hannahrosen57/AdjustaBike-2.0/CAD/exportedCAD/bike.pdf

setPageBoxes("Crop", 0, 0, [0,2000,2000,0]);
TITLE PART NO | bike REVISION DESIGNER | Hannah ENGINEER NOTES

THE INFORMATION AND/OR MATERIAL IN THIS DOCUMENT IS THE PROPERTY OF AND RESTRICTED INFORMATION AND/OR MATERIAL OF THE AUTHOR. THIS INFORMATION MAY NOT BE USED, REPRODUCED, PUBLISHED OR DISCLOSED TO OTHERS WITHOUT WRITTEN AUTHORIZATION. IT IS TO BE USED ONLY FOR MANUFACTURING ITEMS SPECIFIED WITHIN THE DOCUMENT.
