hannahrosen57/AdjustaBike-2.0/PSP/health and safety completed.pdf

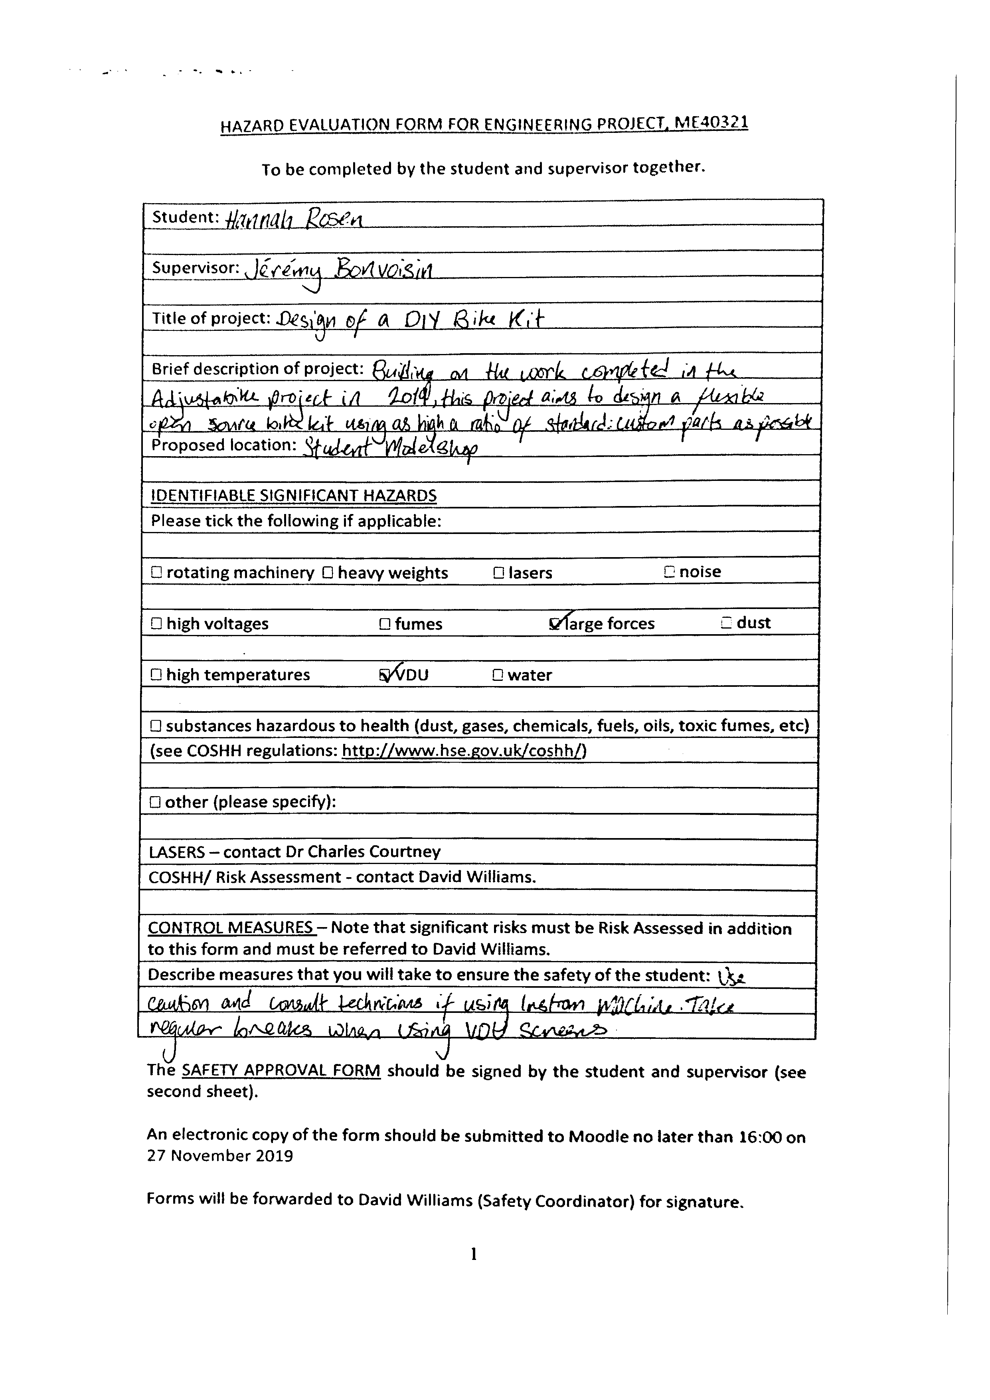
[picture p164: page 1]
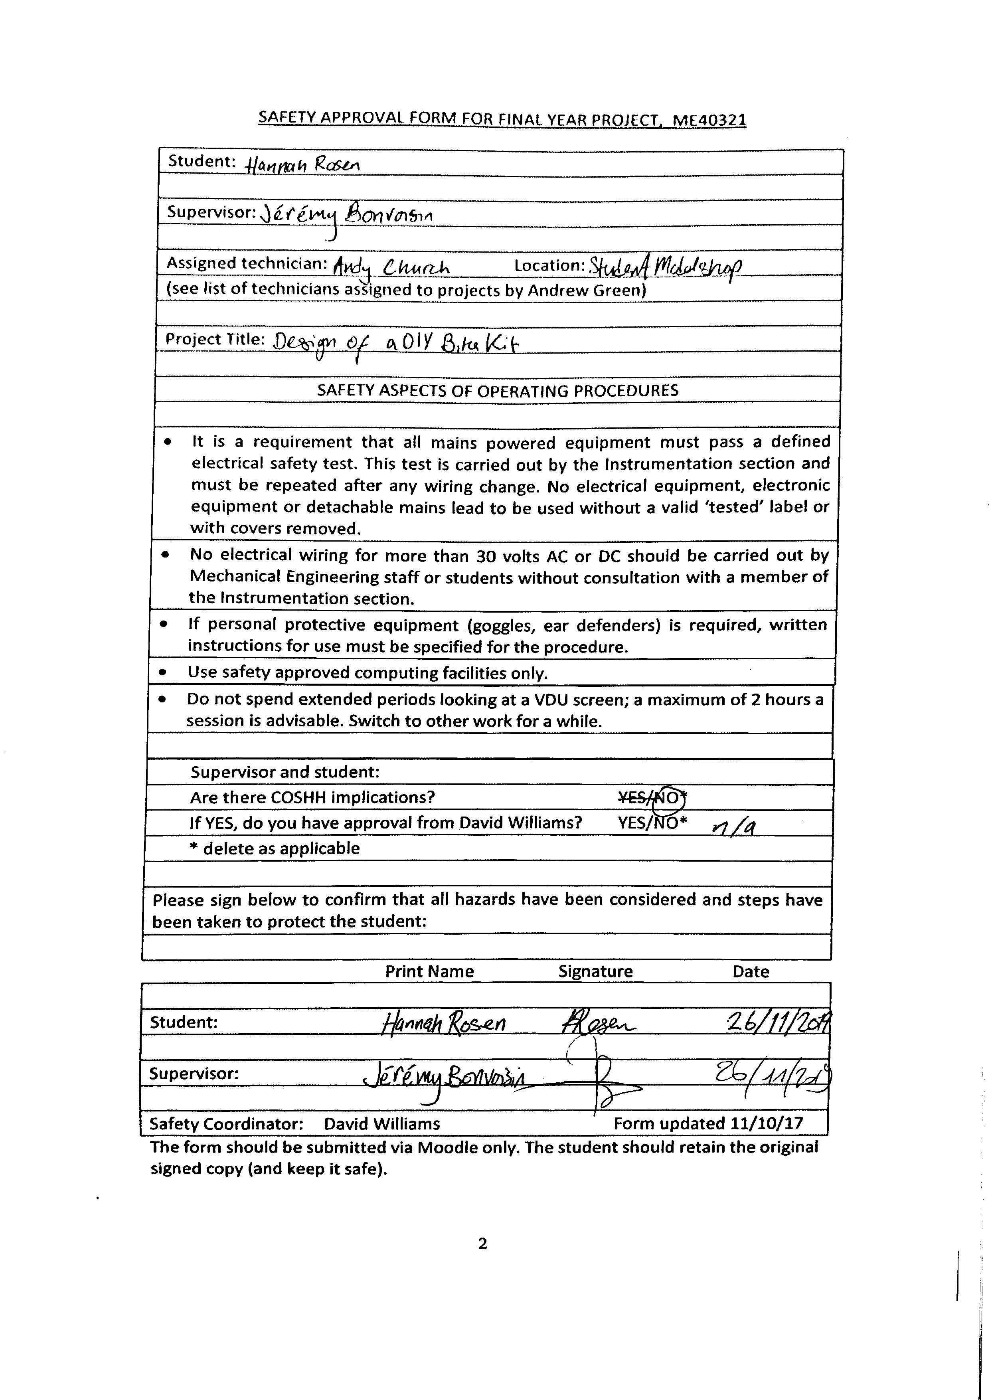
[picture p165: page 2]
