hannahrosen57/AdjustaBike-2.0/CAD/bicycle-wheel-tire-26-inch/2.jpg

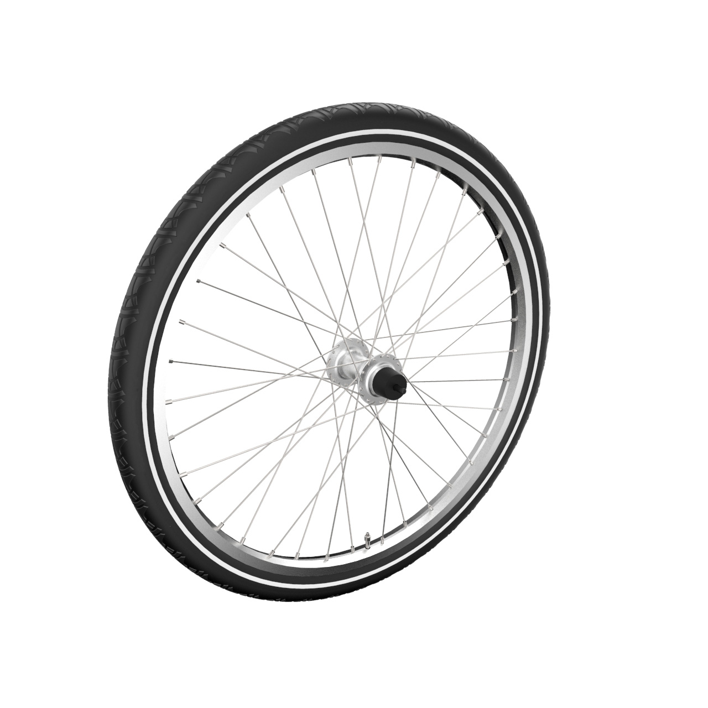
CAD/bicycle-wheel-tire-26-inch/2.jpg
