hannahrosen57/AdjustaBike-2.0/CAD/LW bike.png

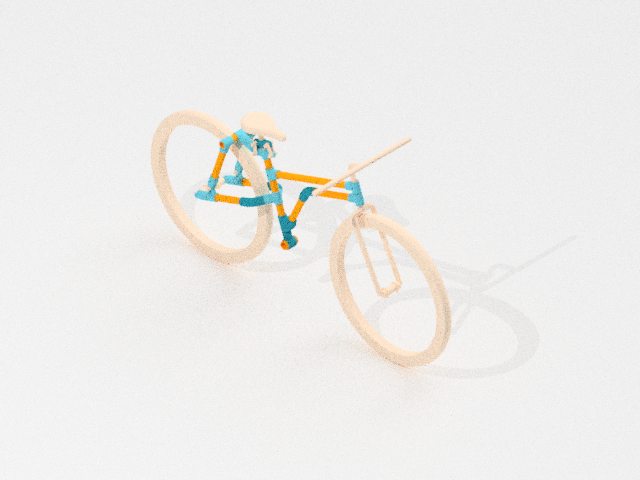
CAD/LW bike.png
