hannahrosen57/AdjustaBike-2.0/CAD/renders/LW bike 1.png

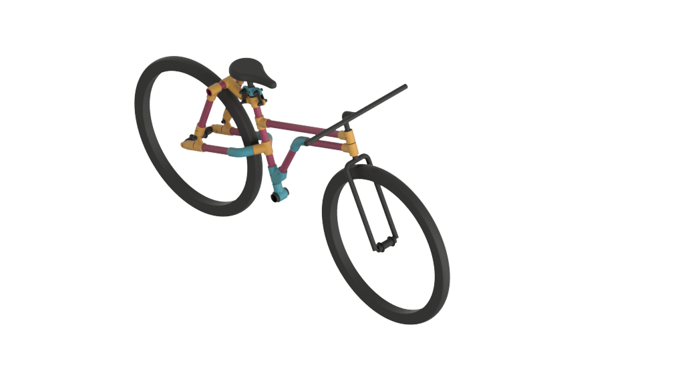
CAD/renders/LW bike 1.png
