hannahrosen57/AdjustaBike-2.0/CAD/renders/LW bike 5.png

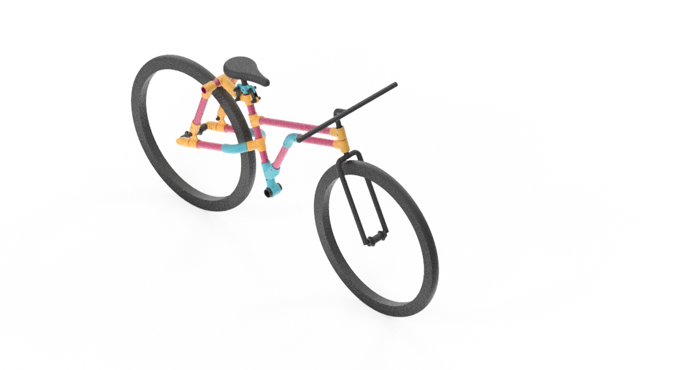
CAD/renders/LW bike 5.png
