hannahrosen57/AdjustaBike-2.0/CAD/Screen Shot 2020-05-14 at 21.41.56.png

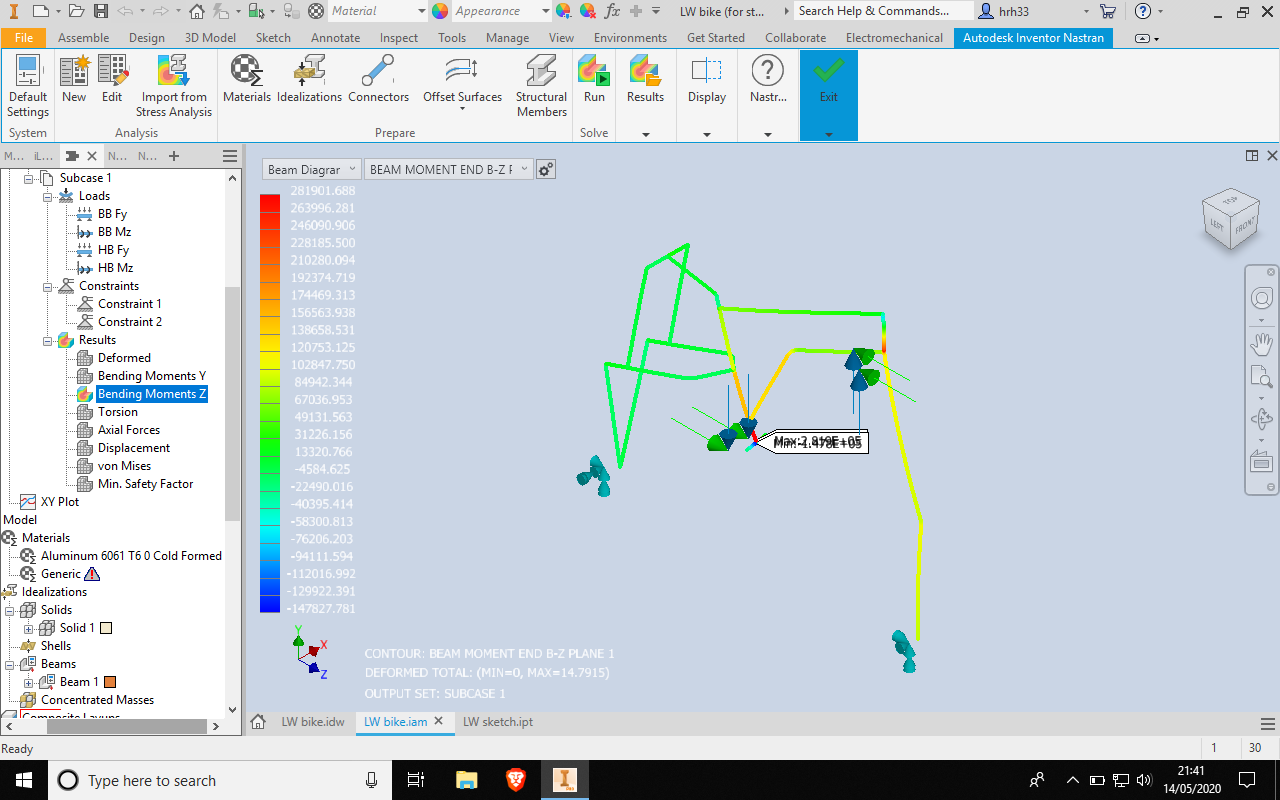
CAD/Screen Shot 2020-05-14 at 21.41.56.png
