hannahrosen57/AdjustaBike-2.0/CAD/screenshots/angle tee.png

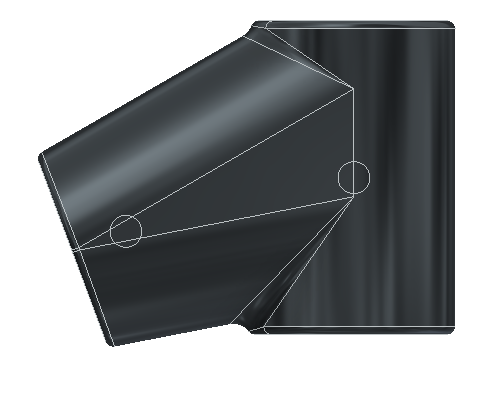
CAD/screenshots/angle tee.png
