hannahrosen57/AdjustaBike-2.0/CAD/screenshots/axial forces.png

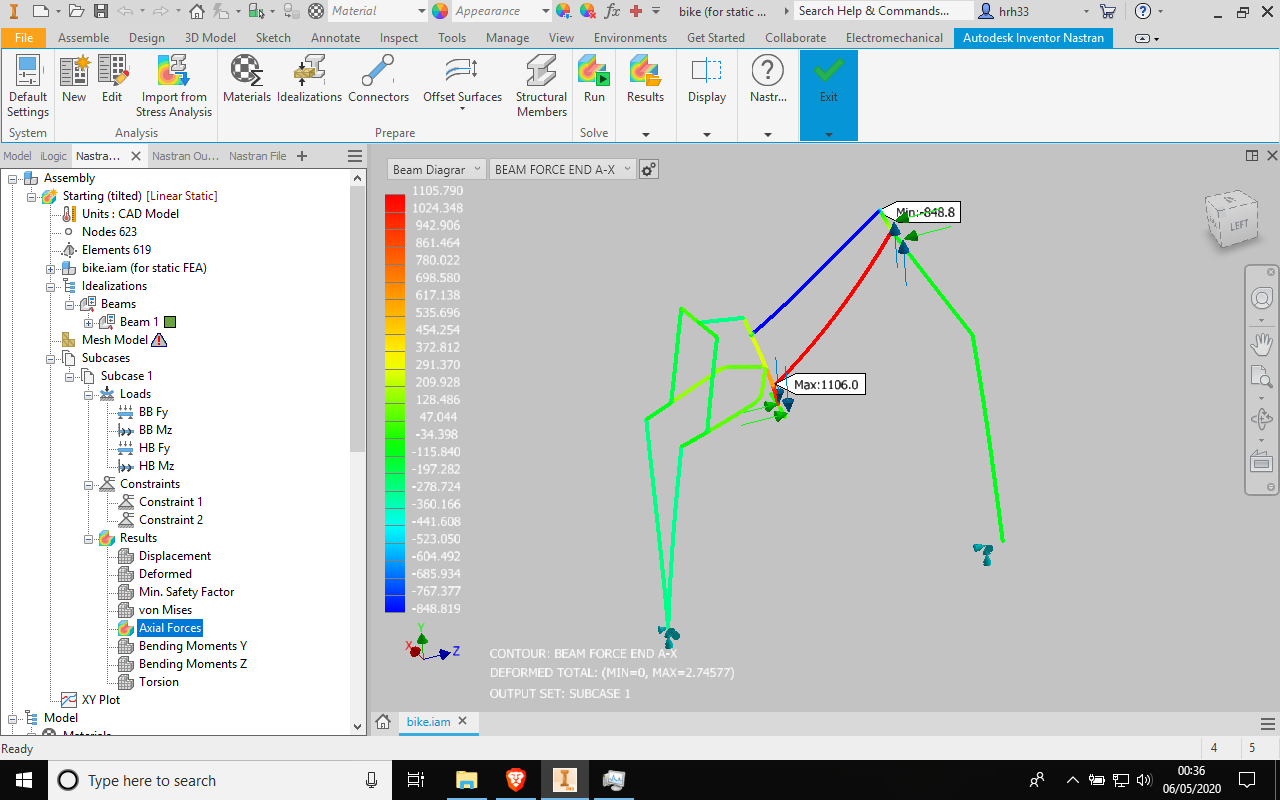
CAD/screenshots/axial forces.png
