hannahrosen57/AdjustaBike-2.0/CAD/screenshots/bike mesh.png

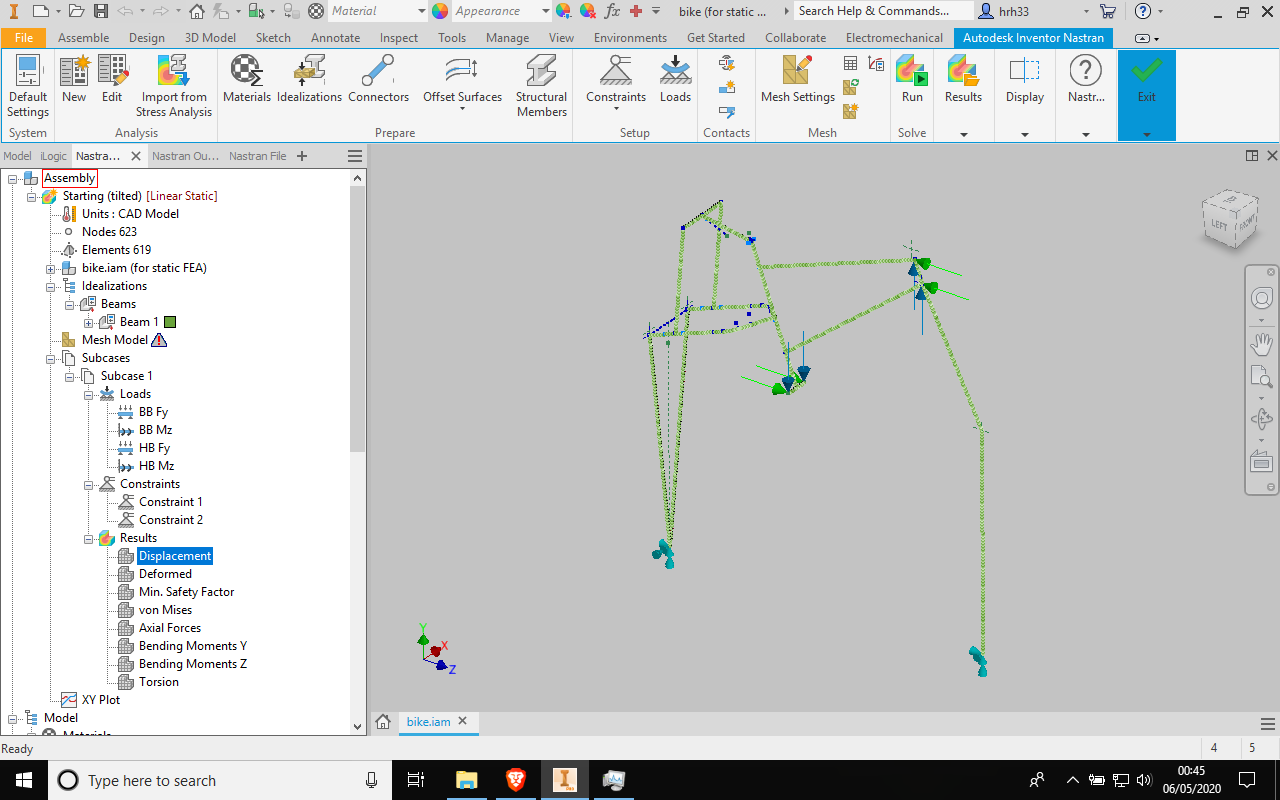
CAD/screenshots/bike mesh.png
