hannahrosen57/AdjustaBike-2.0/CAD/screenshots/disp.png

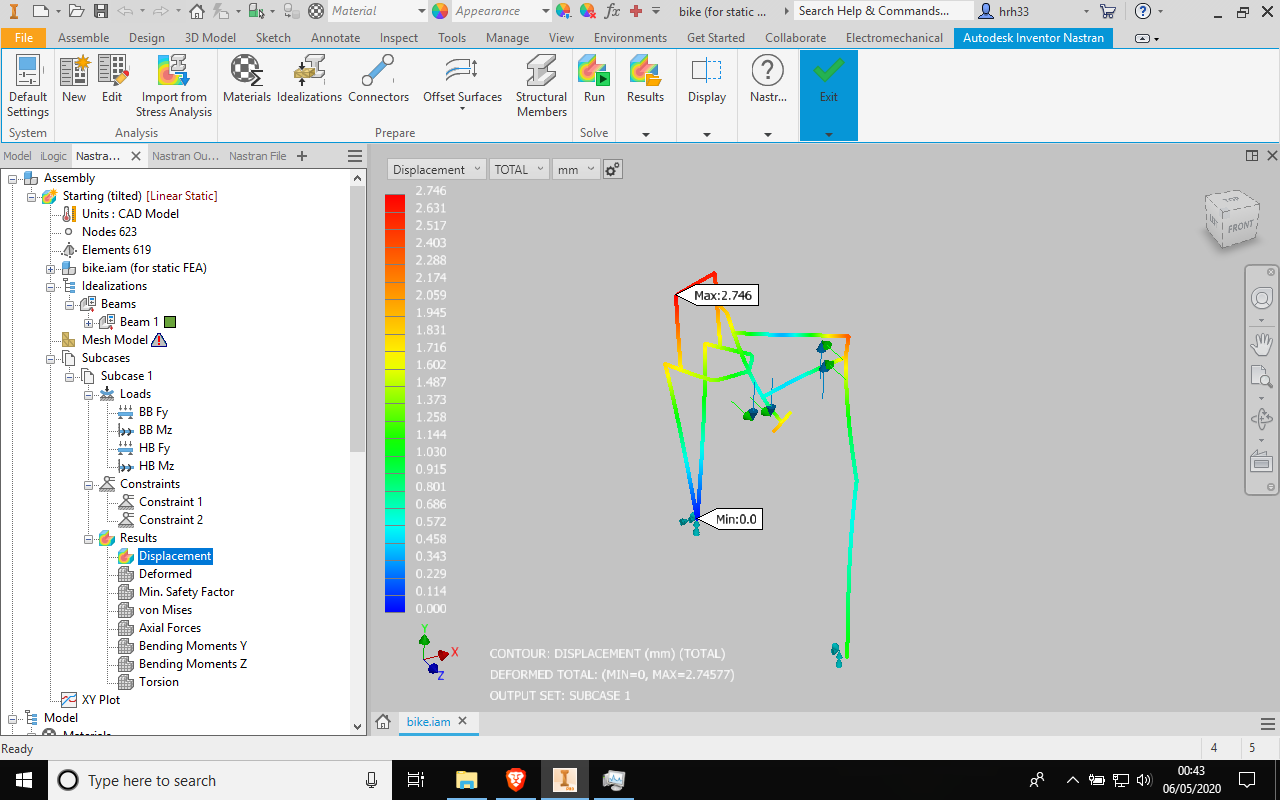
CAD/screenshots/disp.png
