hannahrosen57/AdjustaBike-2.0/CAD/screenshots/open part files.png

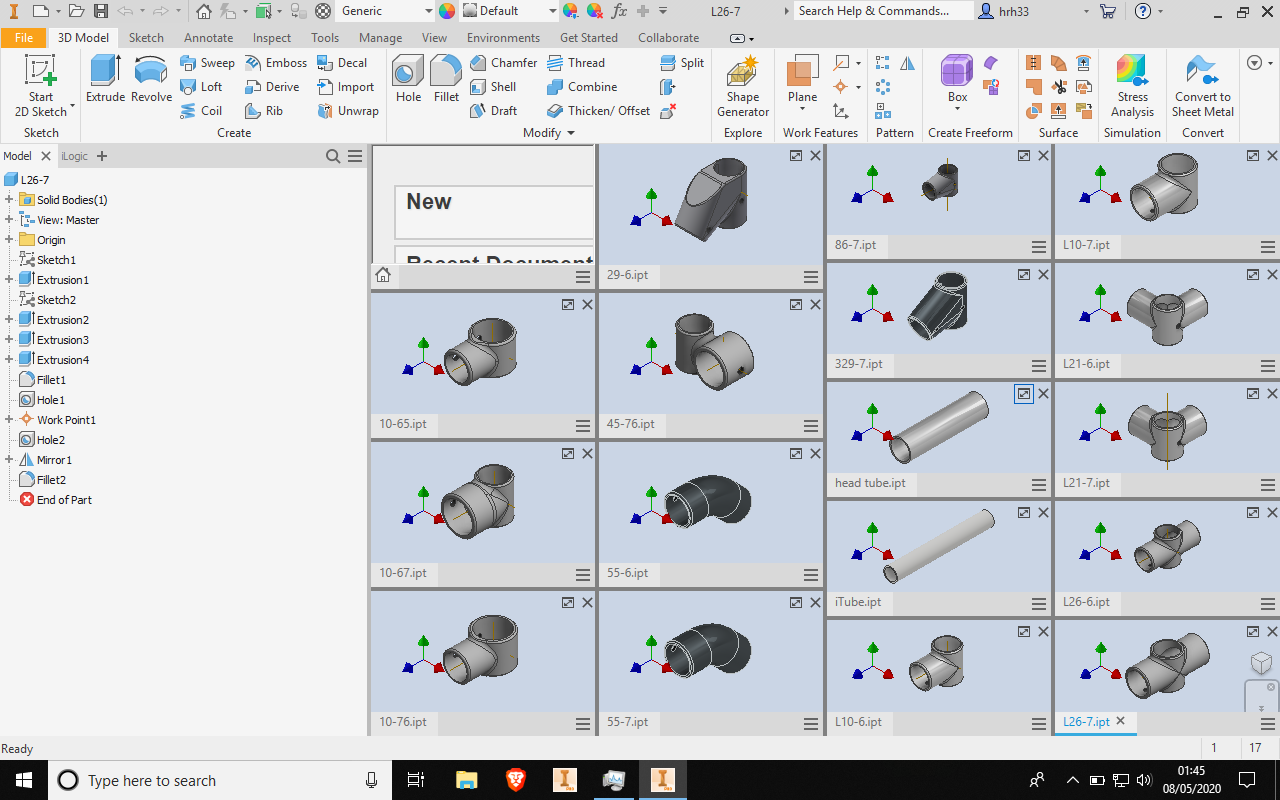
CAD/screenshots/open part files.png
