hannahrosen57/AdjustaBike-2.0/CAD/screenshots/sf closeup.png

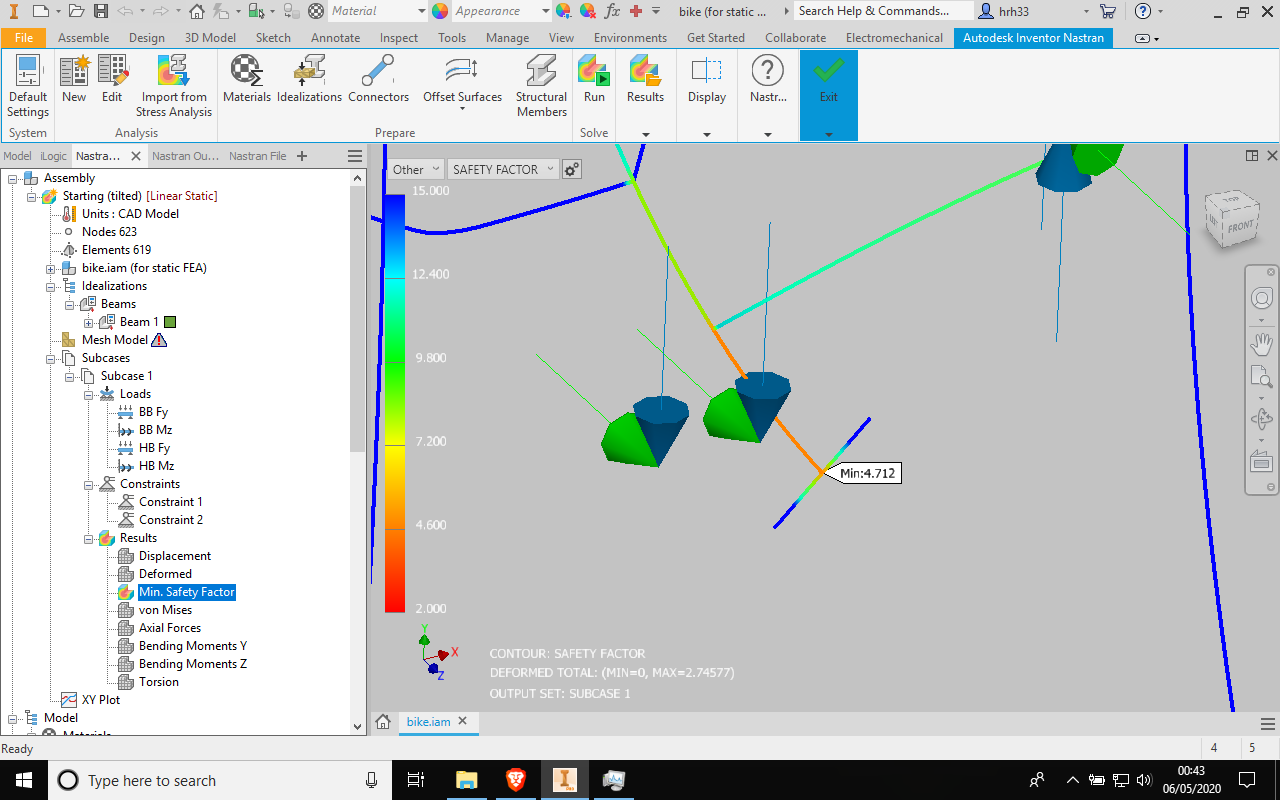
CAD/screenshots/sf closeup.png
