hannahrosen57/AdjustaBike-2.0/CAD/screenshots/sf.png

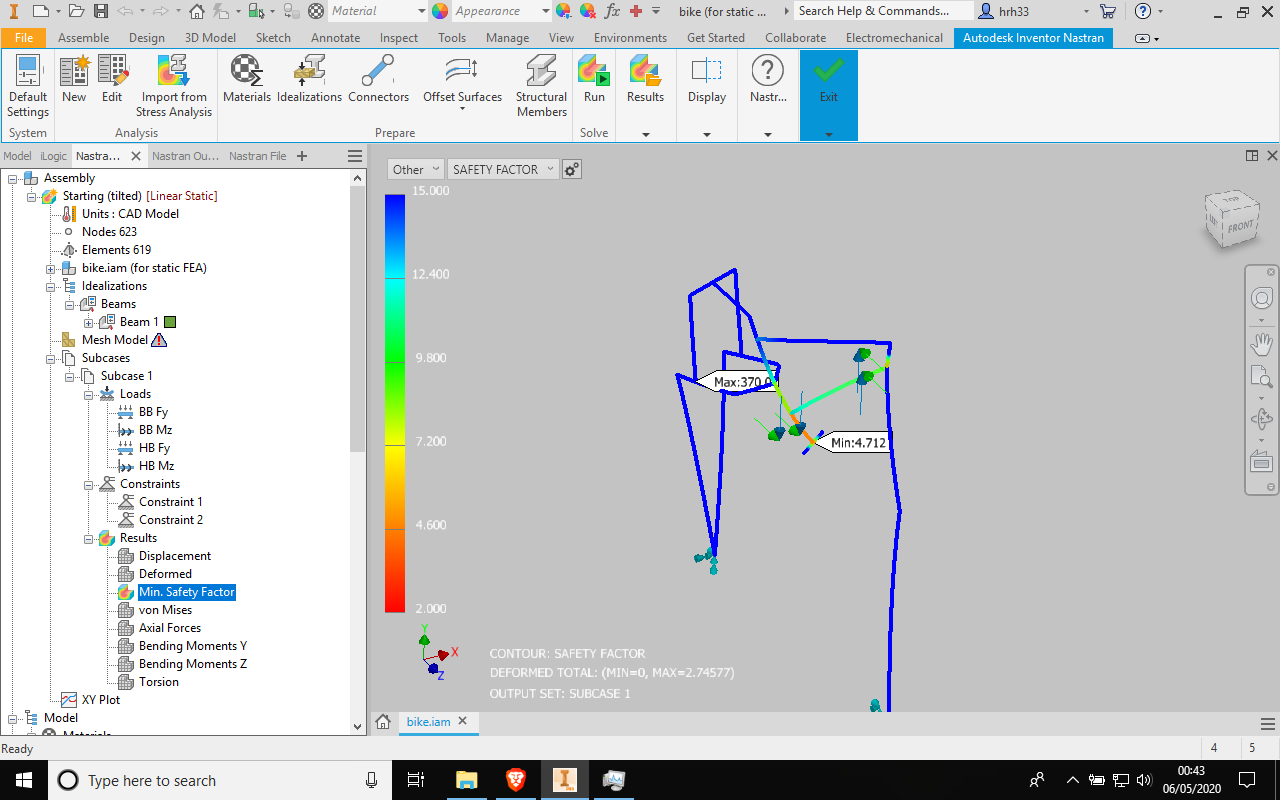
CAD/screenshots/sf.png
