hannahrosen57/AdjustaBike-2.0/CAD/screenshots/von mises 4.png

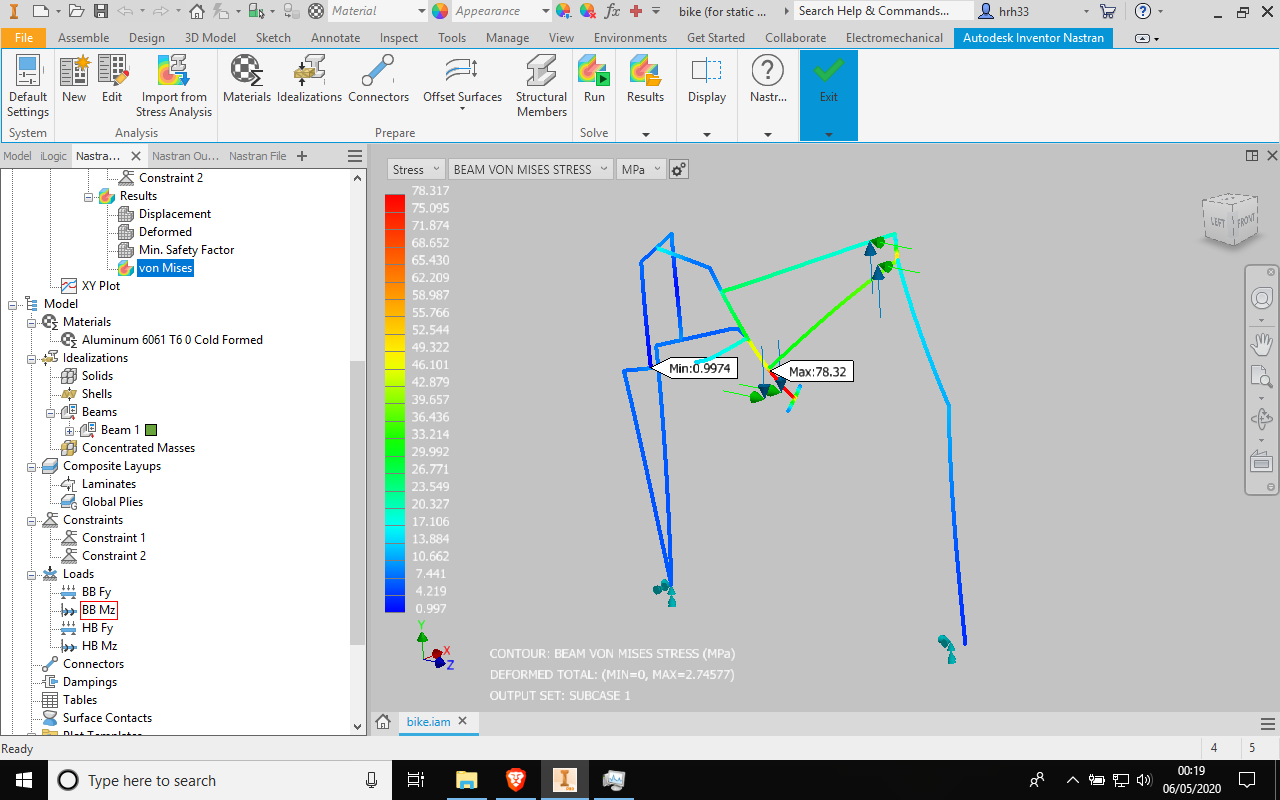
CAD/screenshots/von mises 4.png
