hannahrosen57/AdjustaBike-2.0/CAD/screenshots/von mises bike 1.png

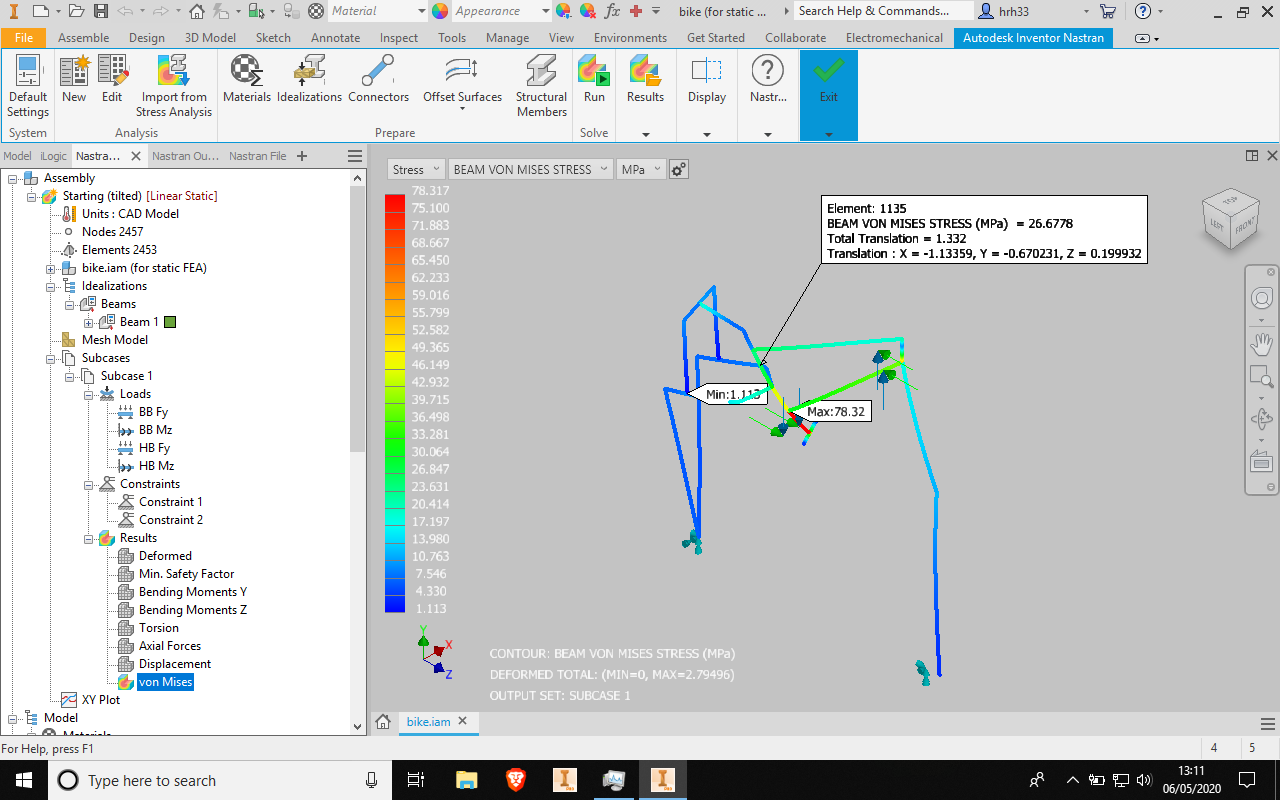
CAD/screenshots/von mises bike 1.png
