hannahrosen57/AdjustaBike-2.0/CAD/screenshots/von mises bike front.png

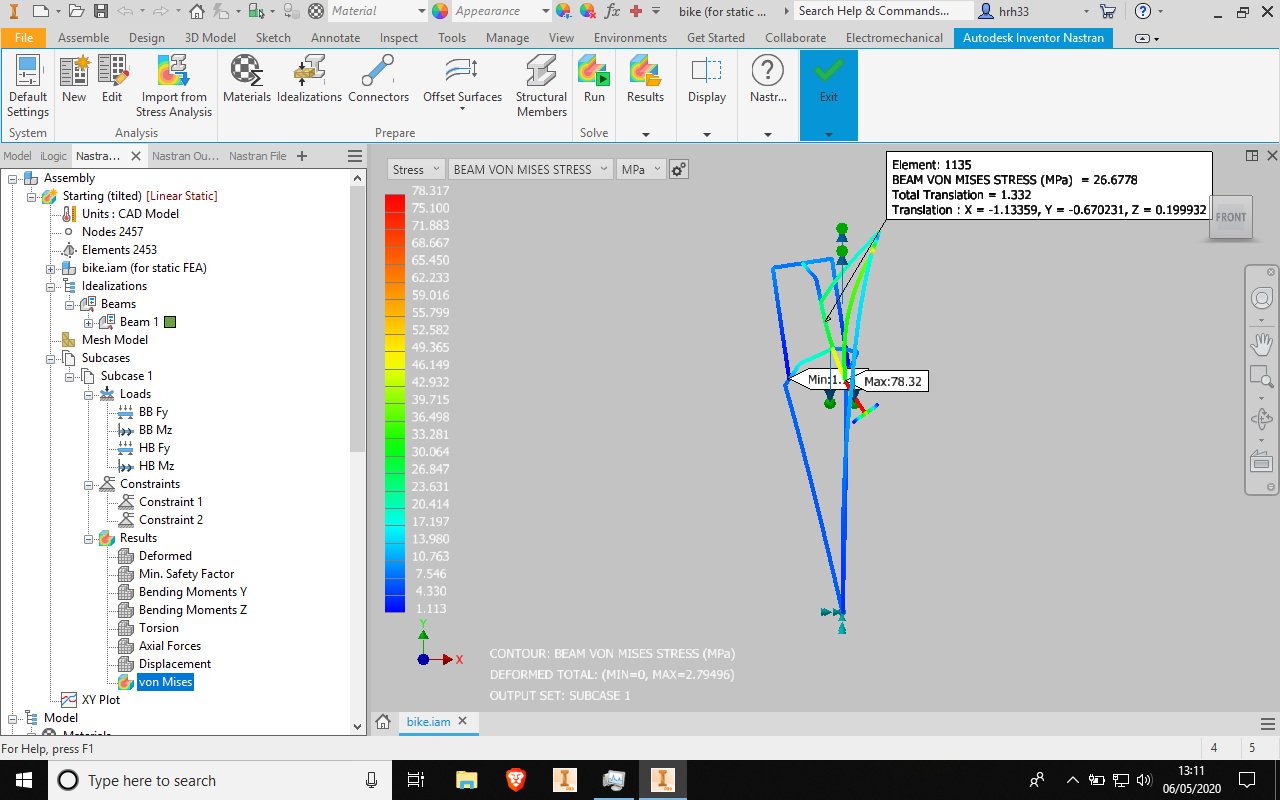
CAD/screenshots/von mises bike front.png
