hannahrosen57/AdjustaBike-2.0/clutter/bicycle frame geometries.png

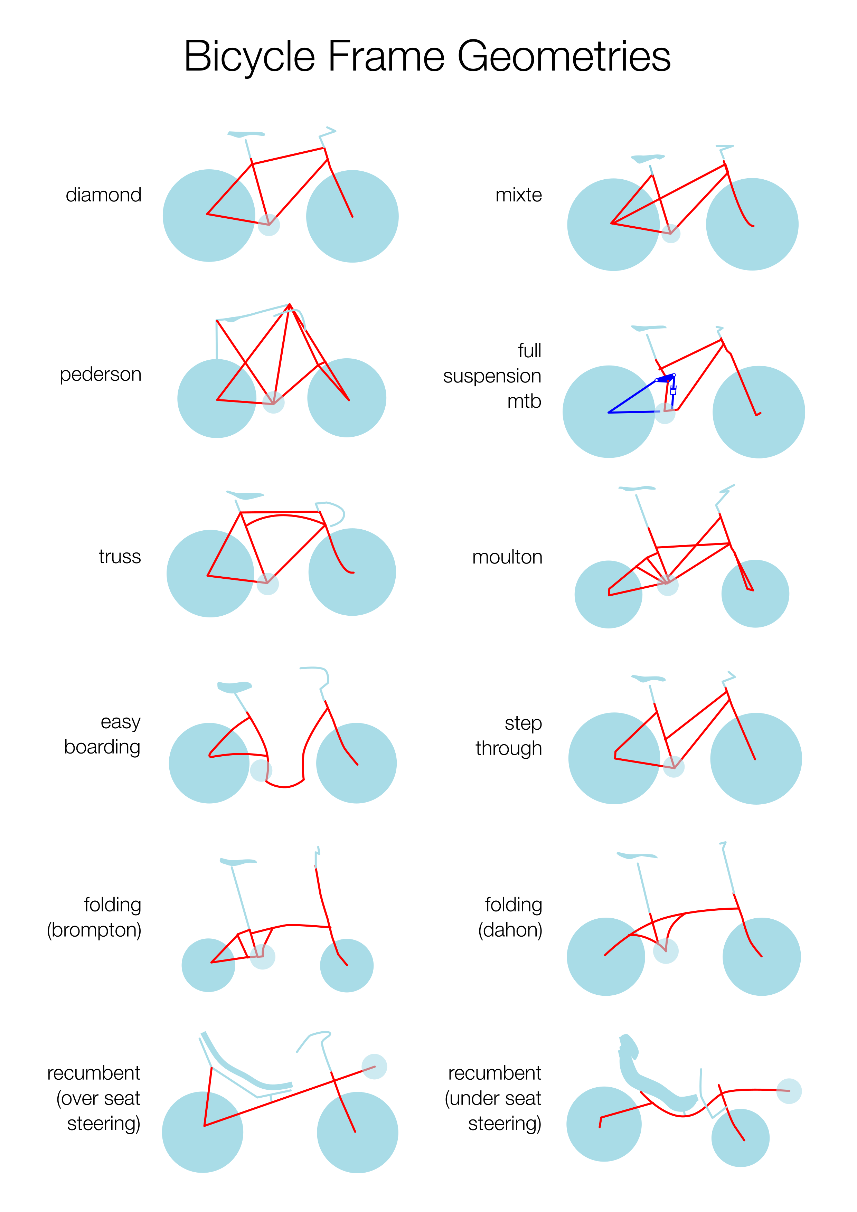
clutter/bicycle frame geometries.png
