hannahrosen57/AdjustaBike-2.0/clutter/cropped_fea1.png

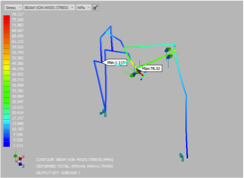
clutter/cropped_fea1.png
