hannahrosen57/AdjustaBike-2.0/clutter/cropped_FEA2.png

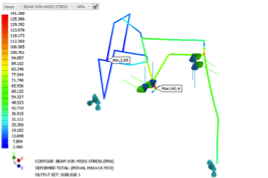
clutter/cropped_FEA2.png
