hannahrosen57/AdjustaBike-2.0/clutter/DIY frame geometries.png

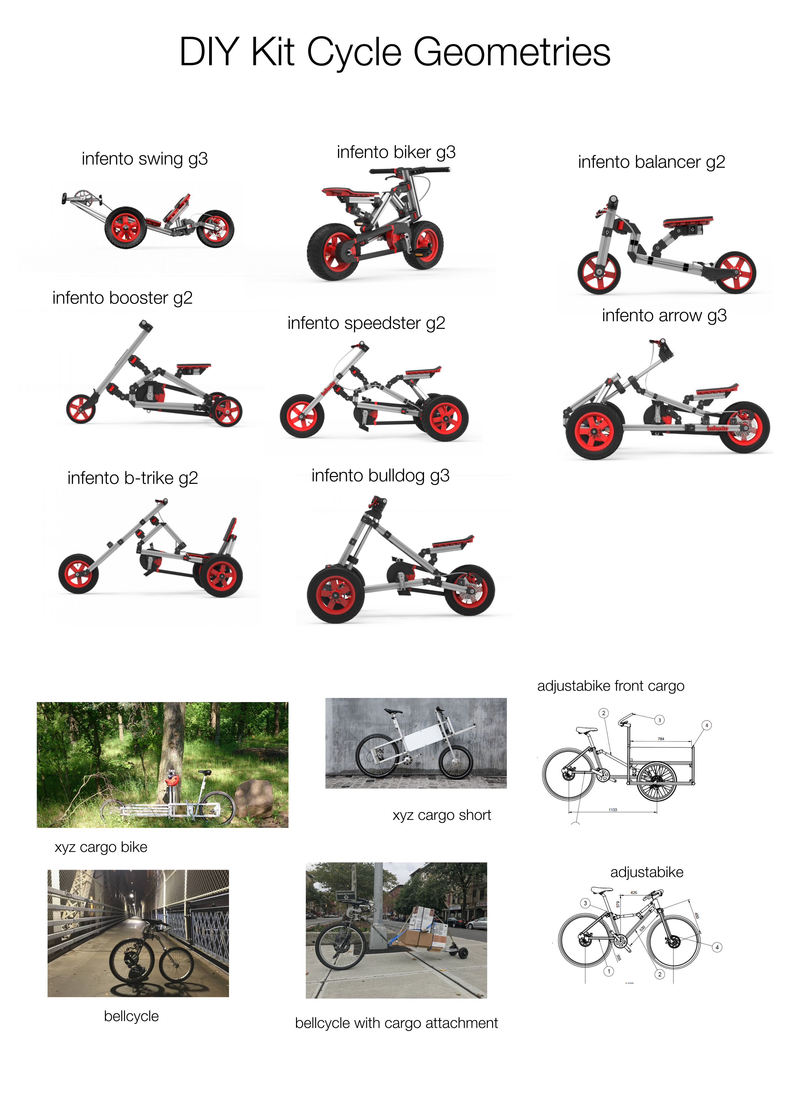
clutter/DIY frame geometries.png
