hannahrosen57/AdjustaBike-2.0/PSP/images/b-trike07-690x449.jpg

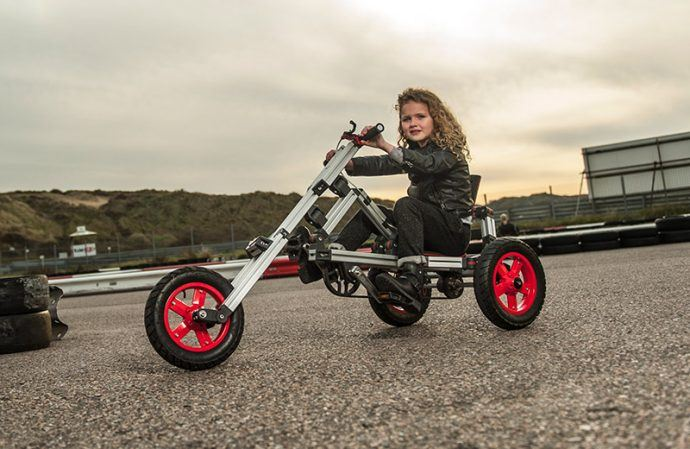
PSP/images/b-trike07-690x449.jpg
