hannahrosen57/AdjustaBike-2.0/PSP/images/bellcycle.PNG

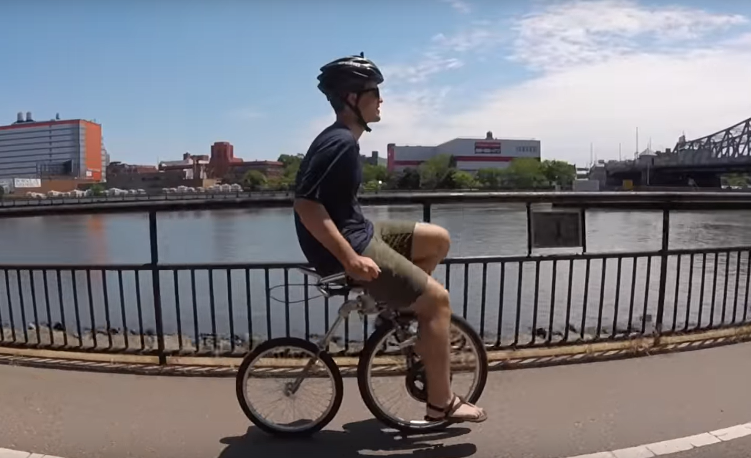
PSP/images/bellcycle.PNG
