hannahrosen57/AdjustaBike-2.0/PSP/images/bulldog12-690x449.jpg

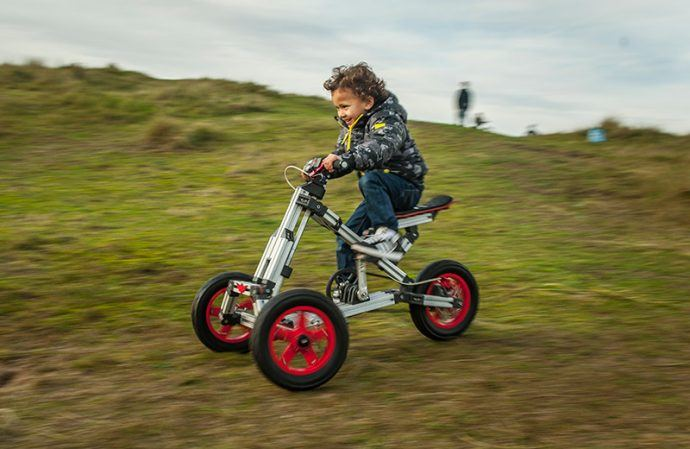
PSP/images/bulldog12-690x449.jpg
