hannahrosen57/AdjustaBike-2.0/PSP/images/obi-bike-flip.png

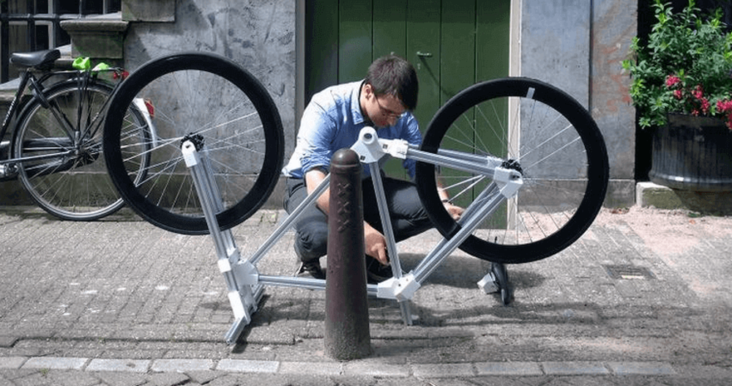
PSP/images/obi-bike-flip.png
