hannahrosen57/AdjustaBike-2.0/PSP/images/parameters.PNG

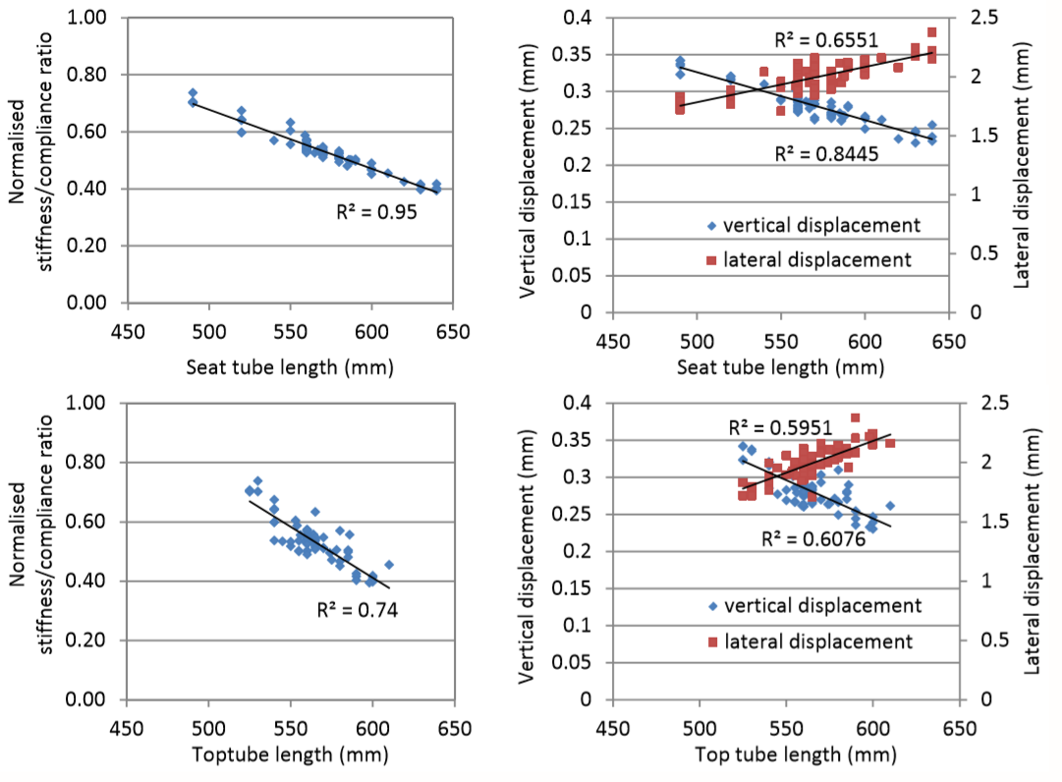
PSP/images/parameters.PNG
