hannahrosen57/AdjustaBike-2.0/PSP/images/skywalker.PNG

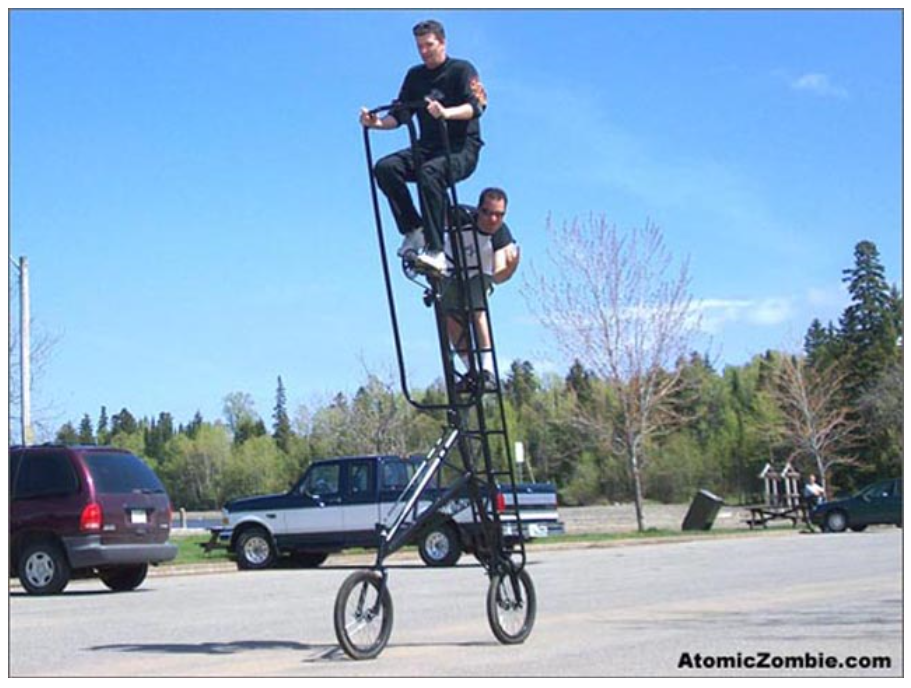
PSP/images/skywalker.PNG
