hannahrosen57/AdjustaBike-2.0/PSP/images/velocar.jpg

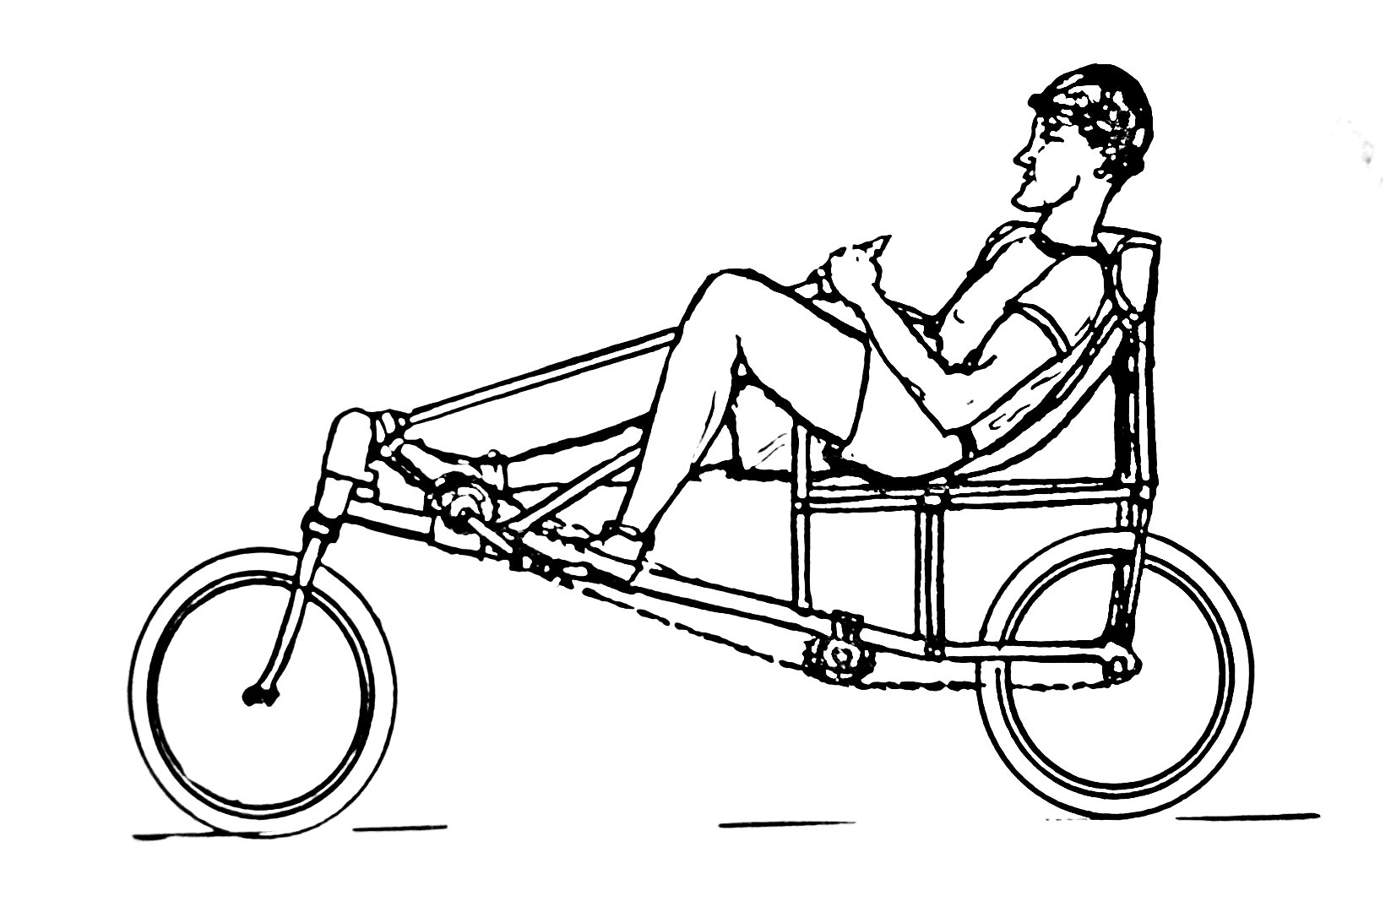
PSP/images/velocar.jpg
