hannahrosen57/AdjustaBike-2.0/PSP/images/XYZ-CARGO-Group1.jpg

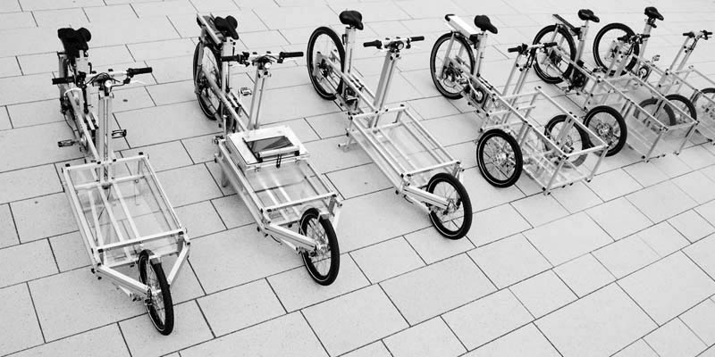
PSP/images/XYZ-CARGO-Group1.jpg
