hannahrosen57/AdjustaBike-2.0/clutter/possible components/Q-CLAMP-JINAN-TUV-LOAD-TABLE-3.pdf

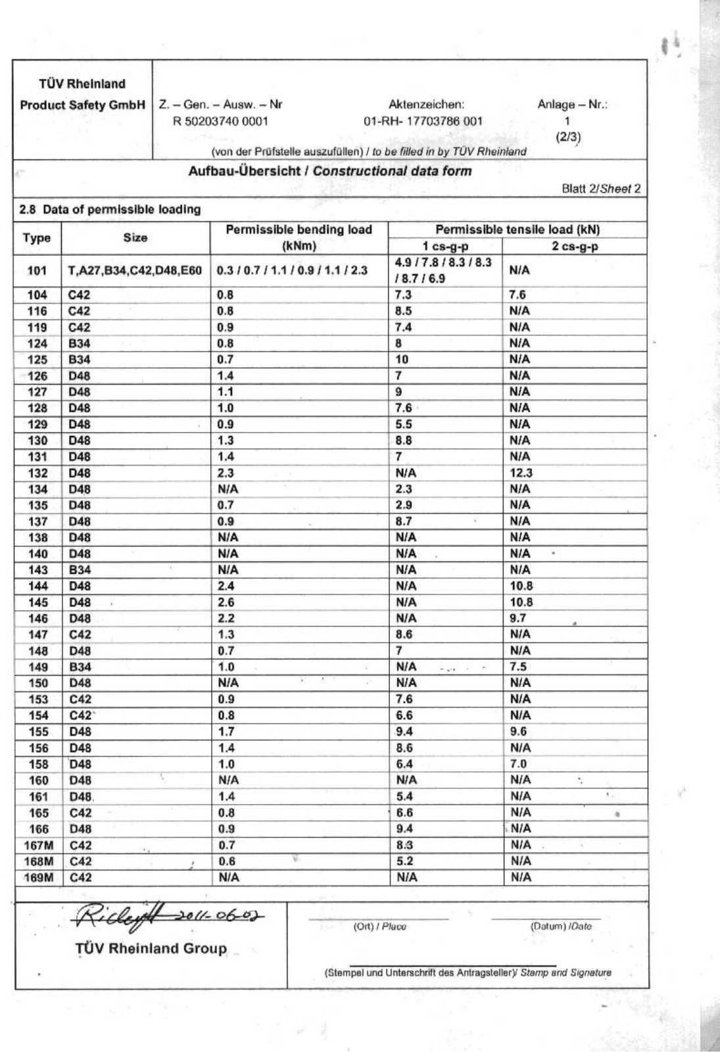
[picture p201: page 1]
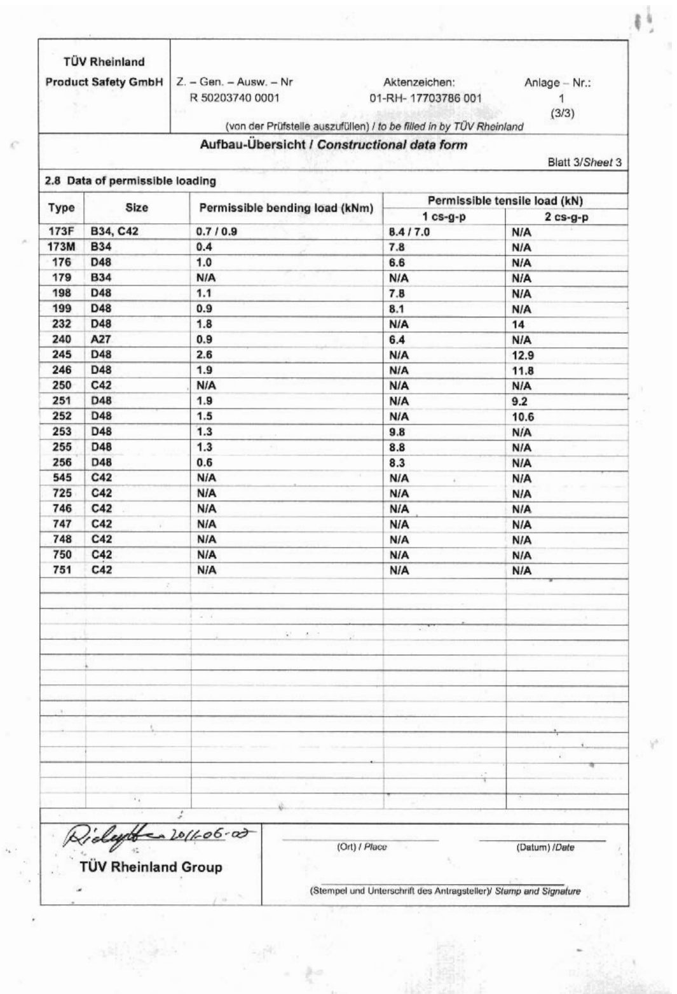
[picture p202: page 2]
