hannahrosen57/AdjustaBike-2.0/clutter/possible components/Qclamp-conversion-table.pdf

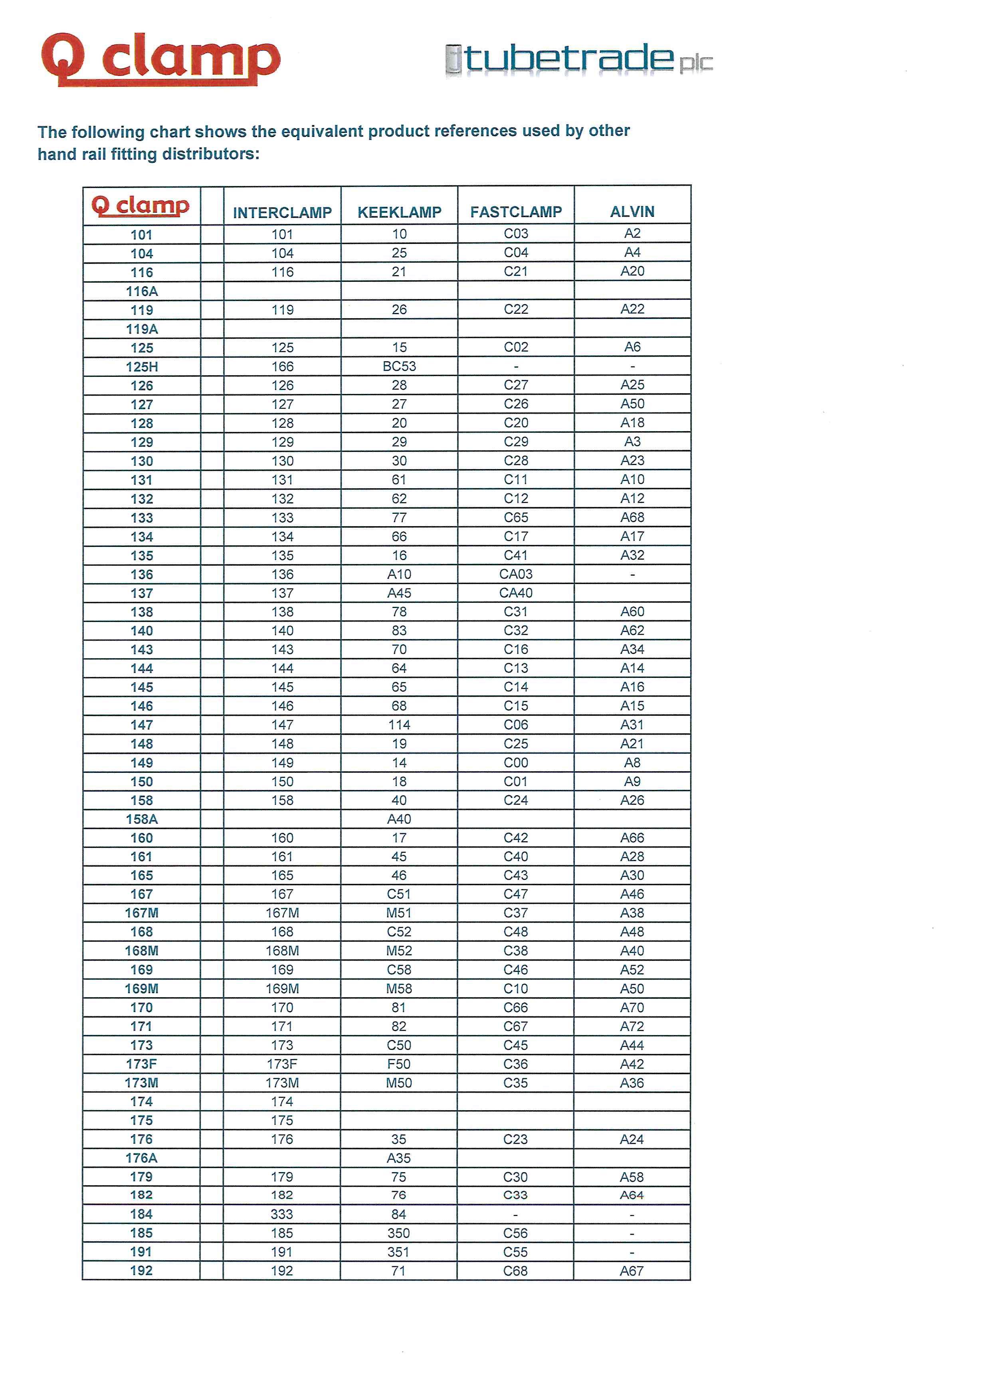
[picture p203: page 1]
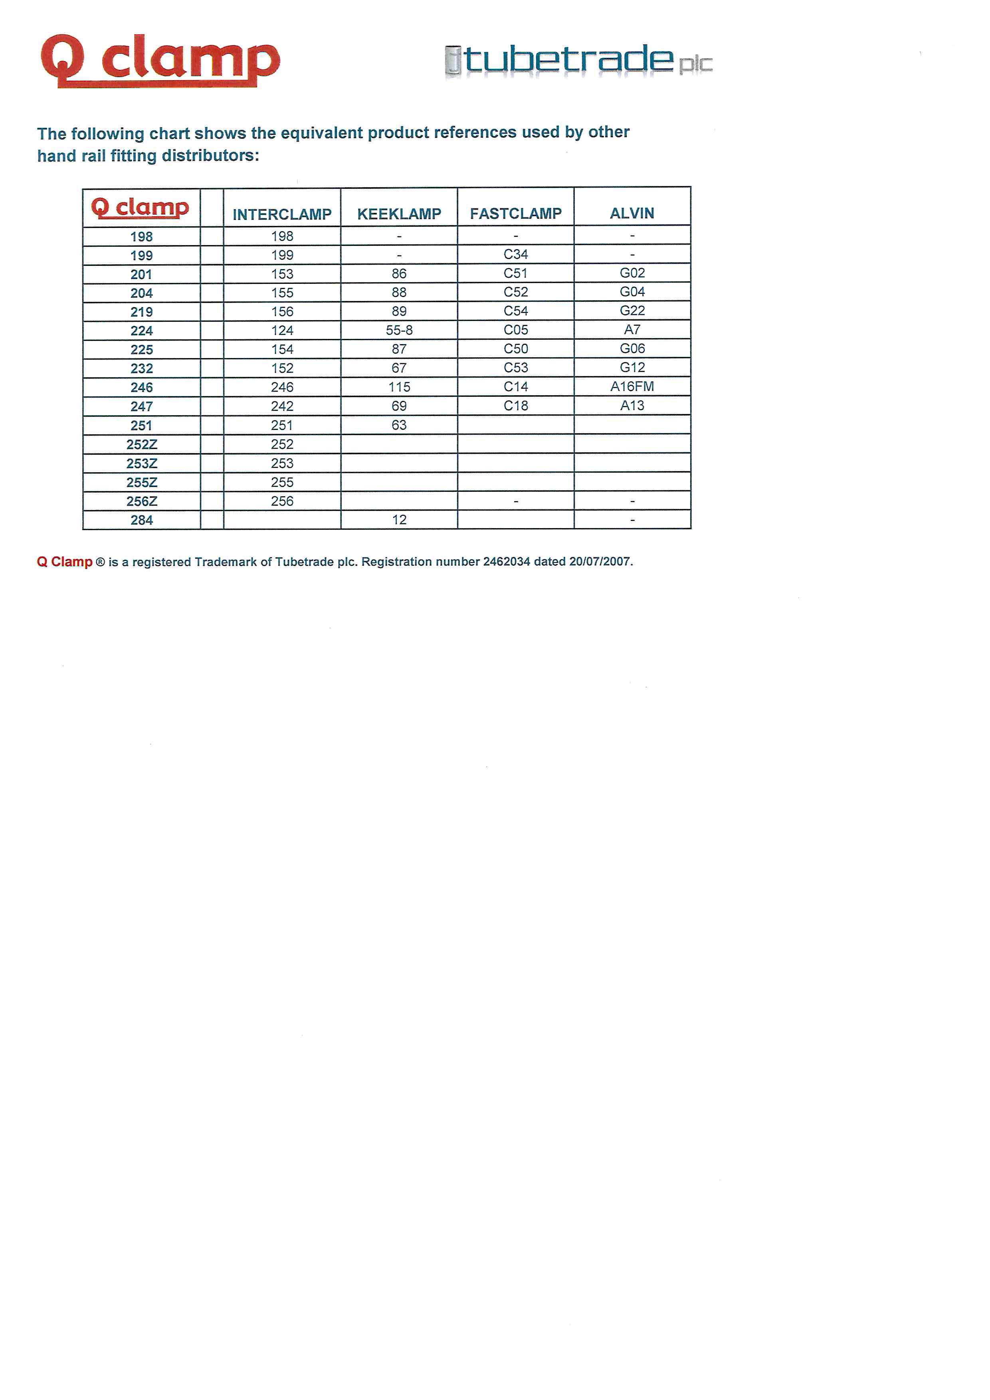
[picture p204: page 2]
