hannahrosen57/AdjustaBike-2.0/clutter/possible components/Kee/ENGLISH KEE KLAMP TUV - 2015.pdf

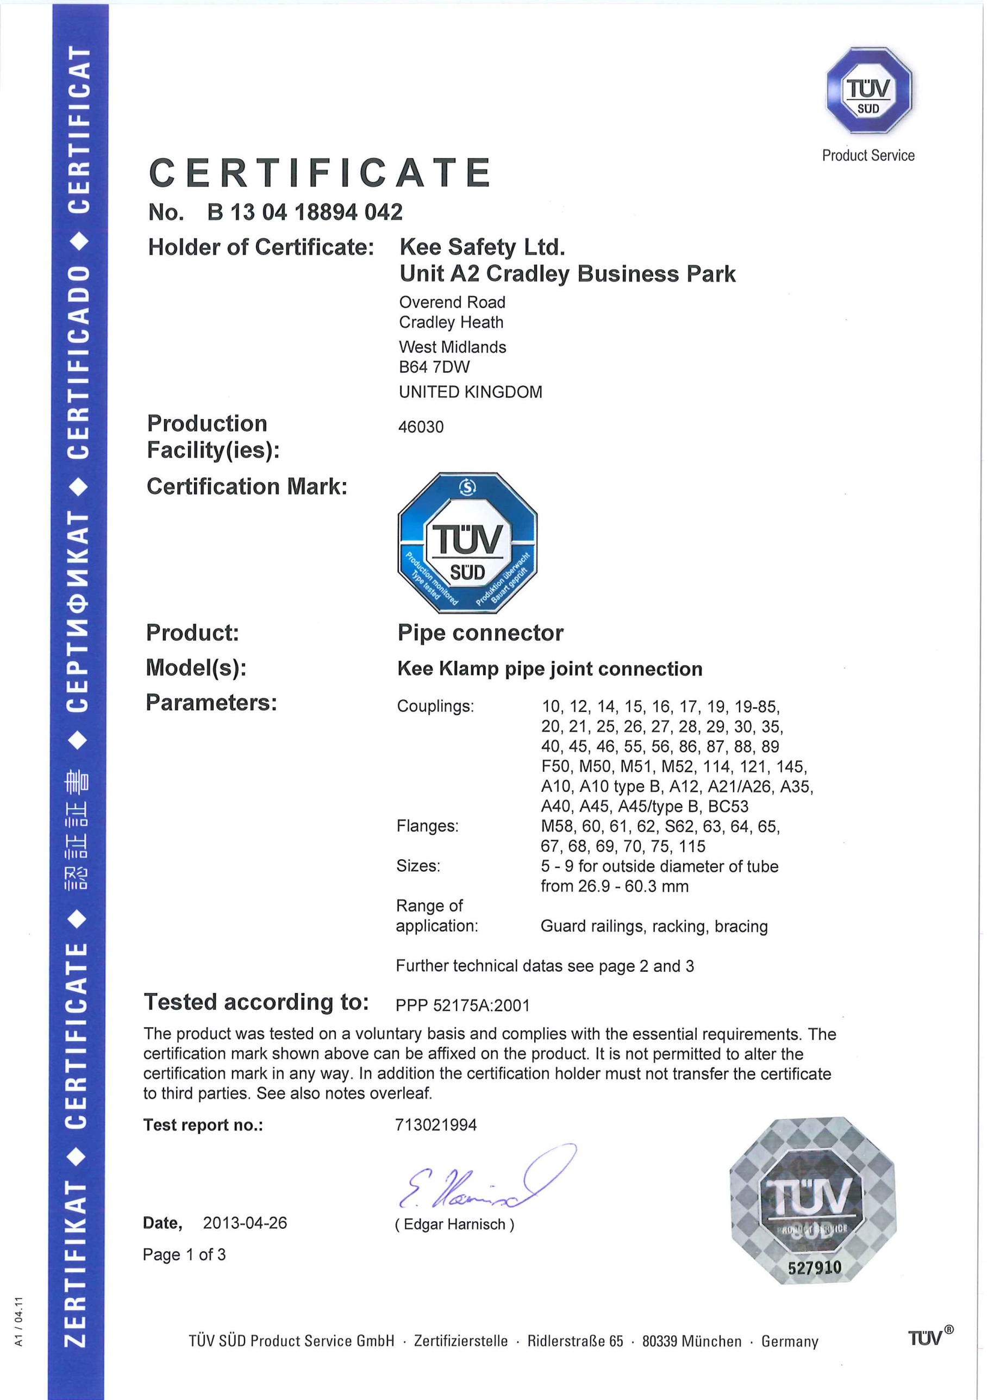
[picture p205: page 1]
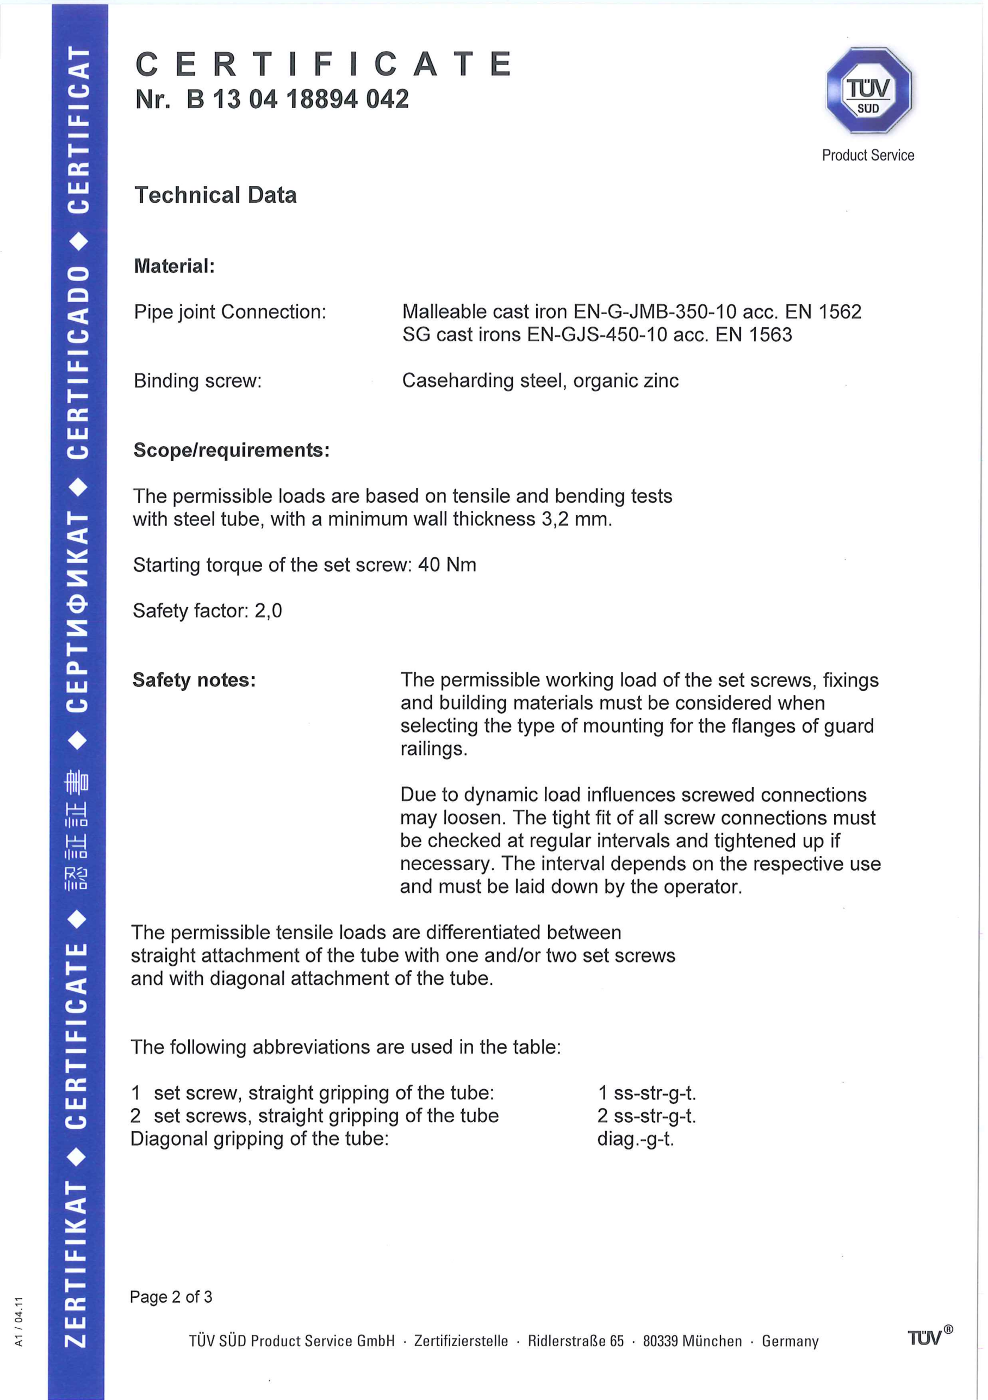
[picture p206: page 2]
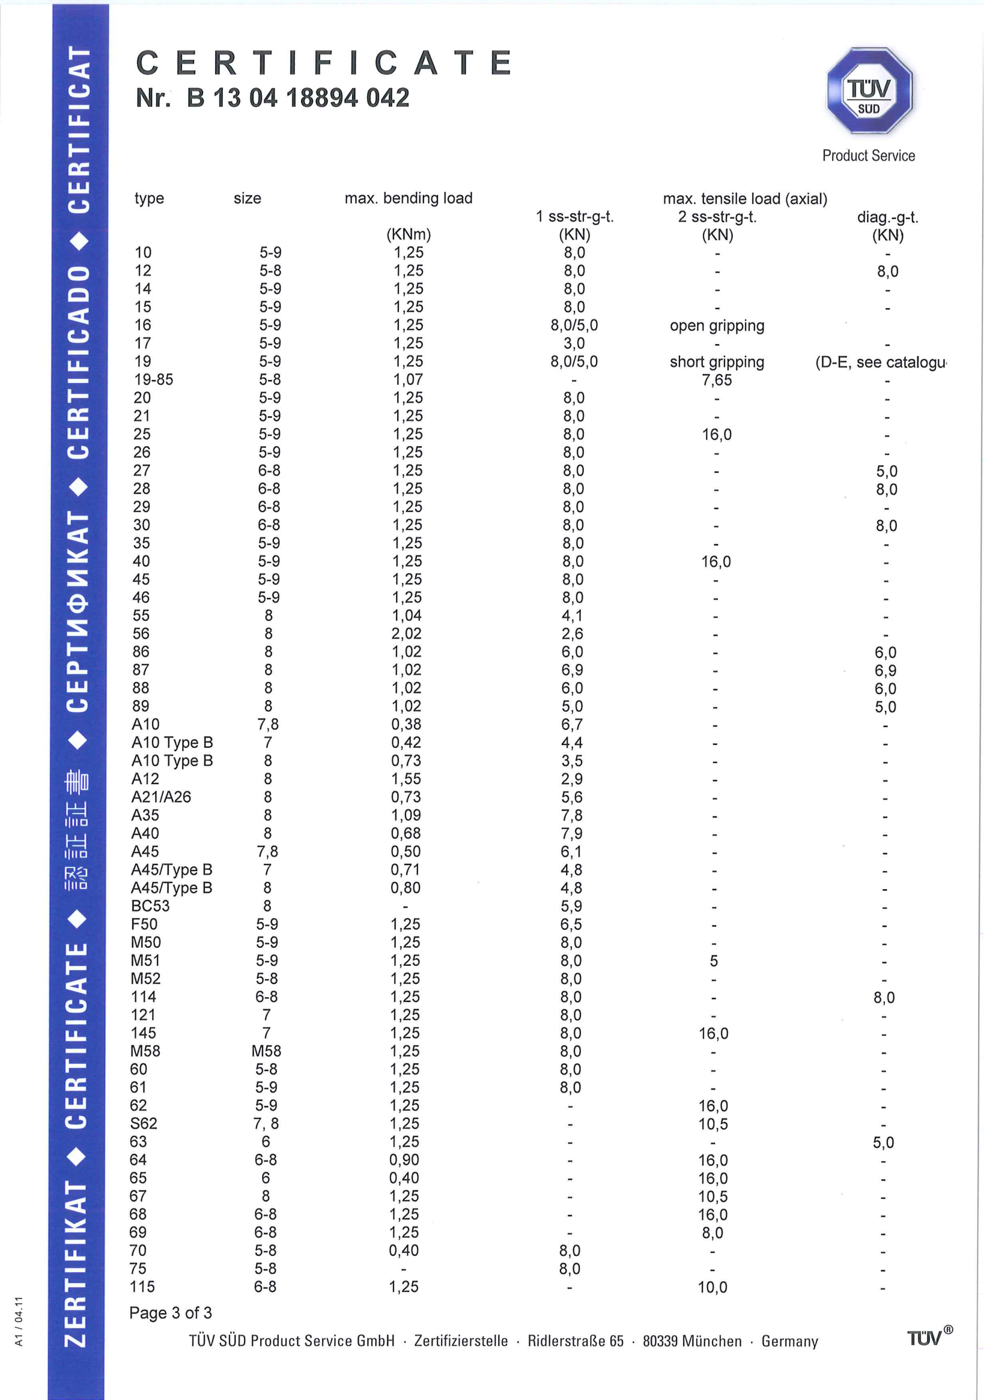
[picture p207: page 3]
