hannahrosen57/AdjustaBike-2.0/clutter/possible components/Kee/TUV KL.pdf

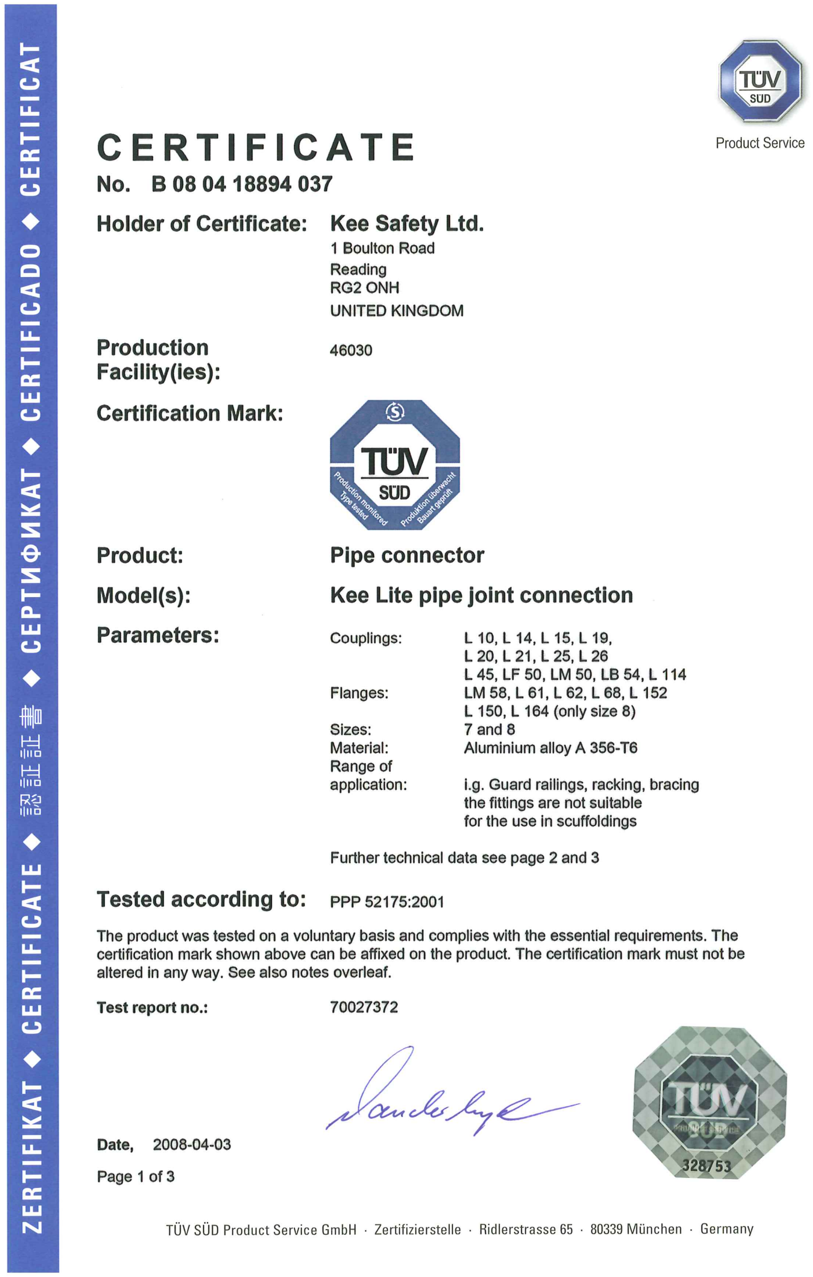
[picture p208: page 1]
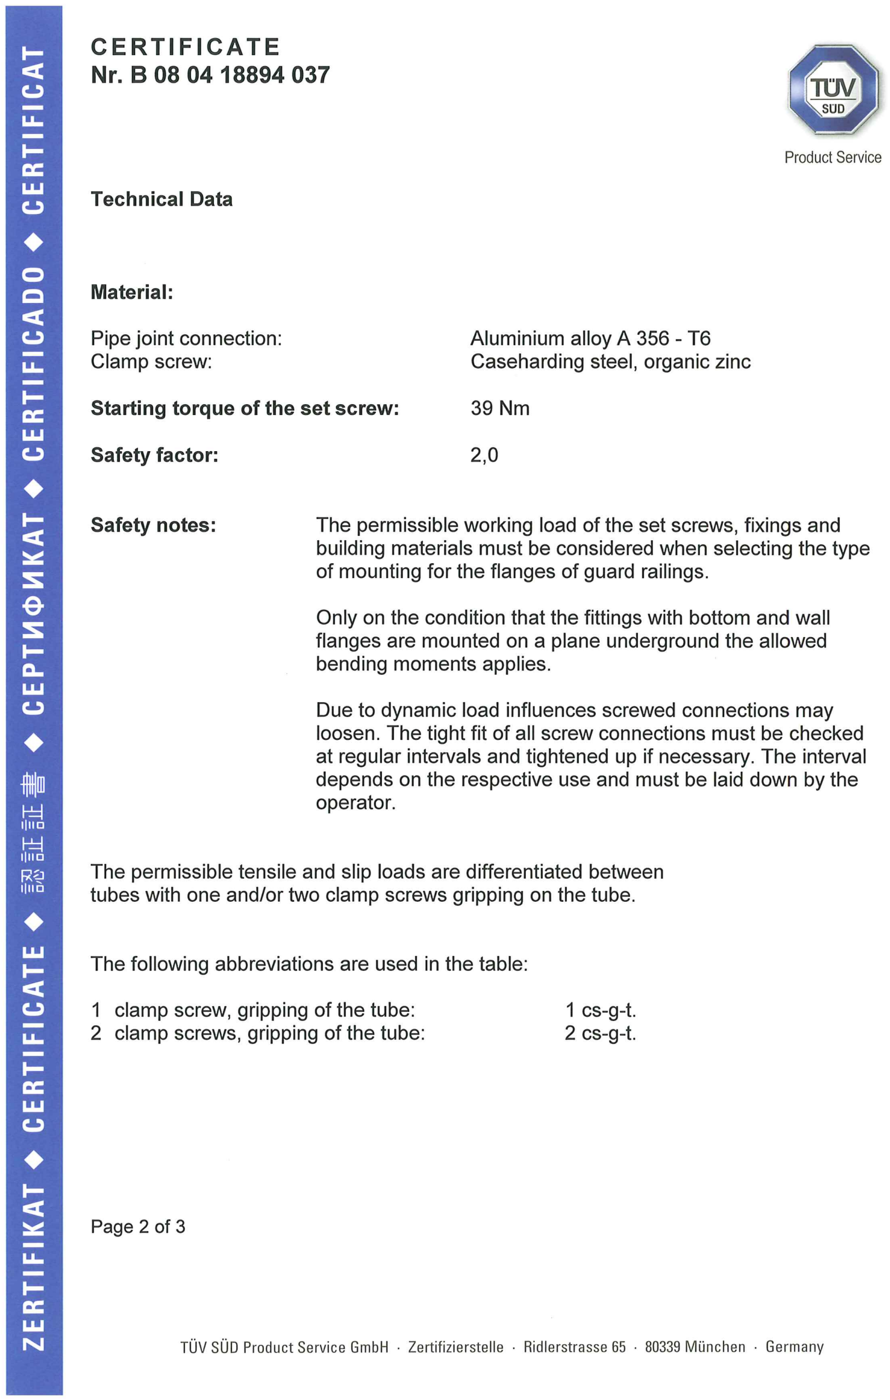
[picture p209: page 2]
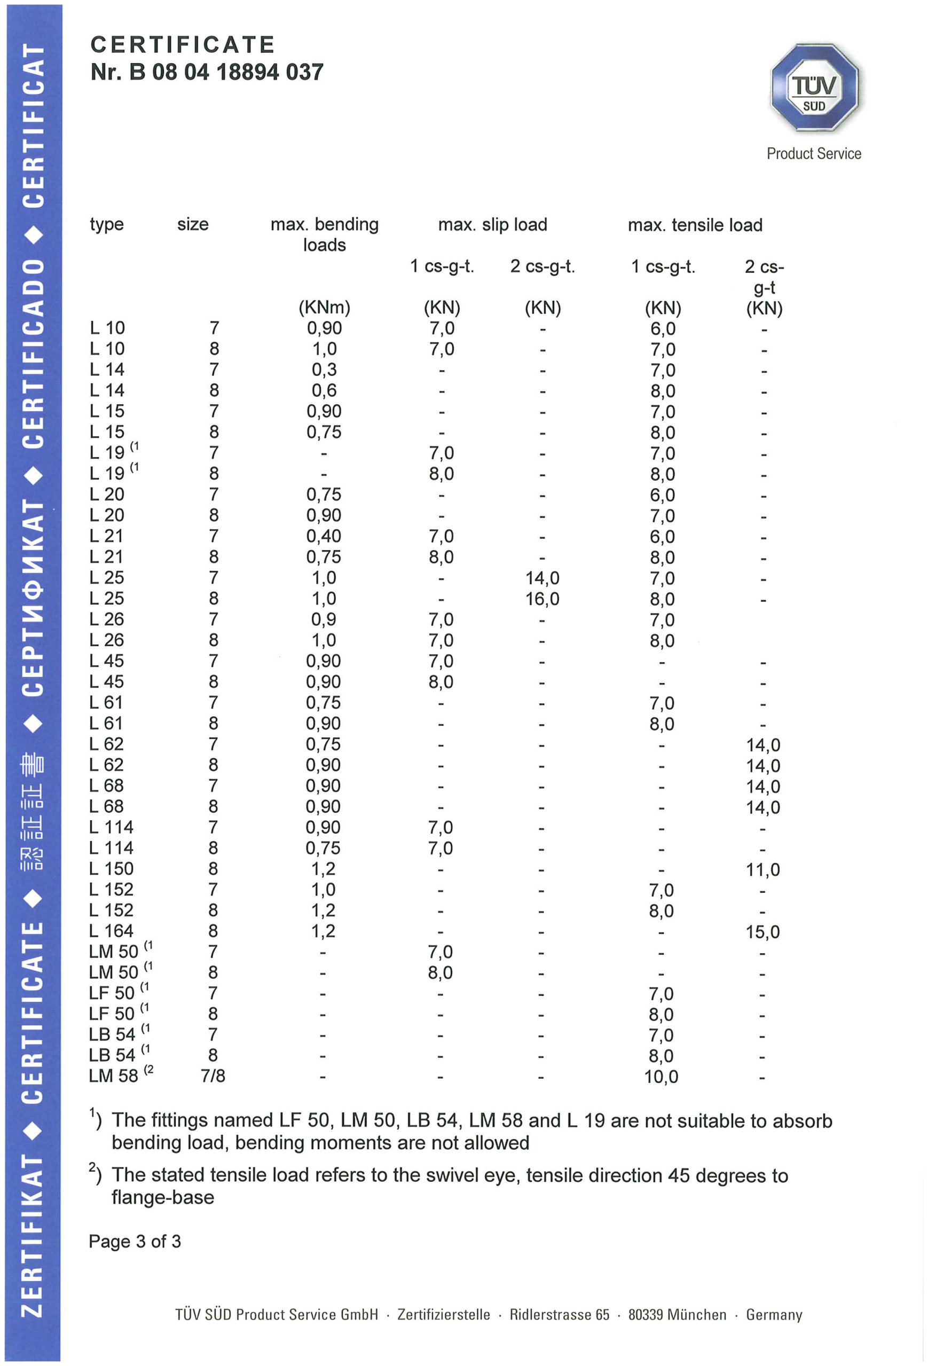
[picture p210: page 3]
