hannahrosen57/AdjustaBike-2.0/PSP/images/instructions.PNG

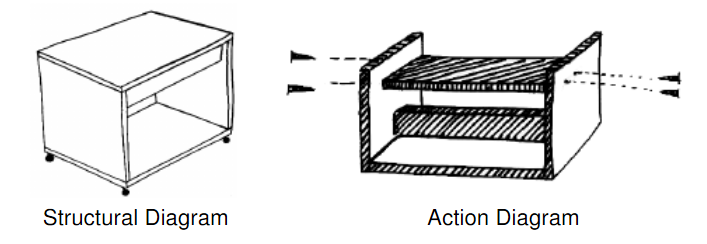
PSP/images/instructions.PNG
