hannahrosen57/AdjustaBike-2.0/CAD/LINK 4.pdf

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

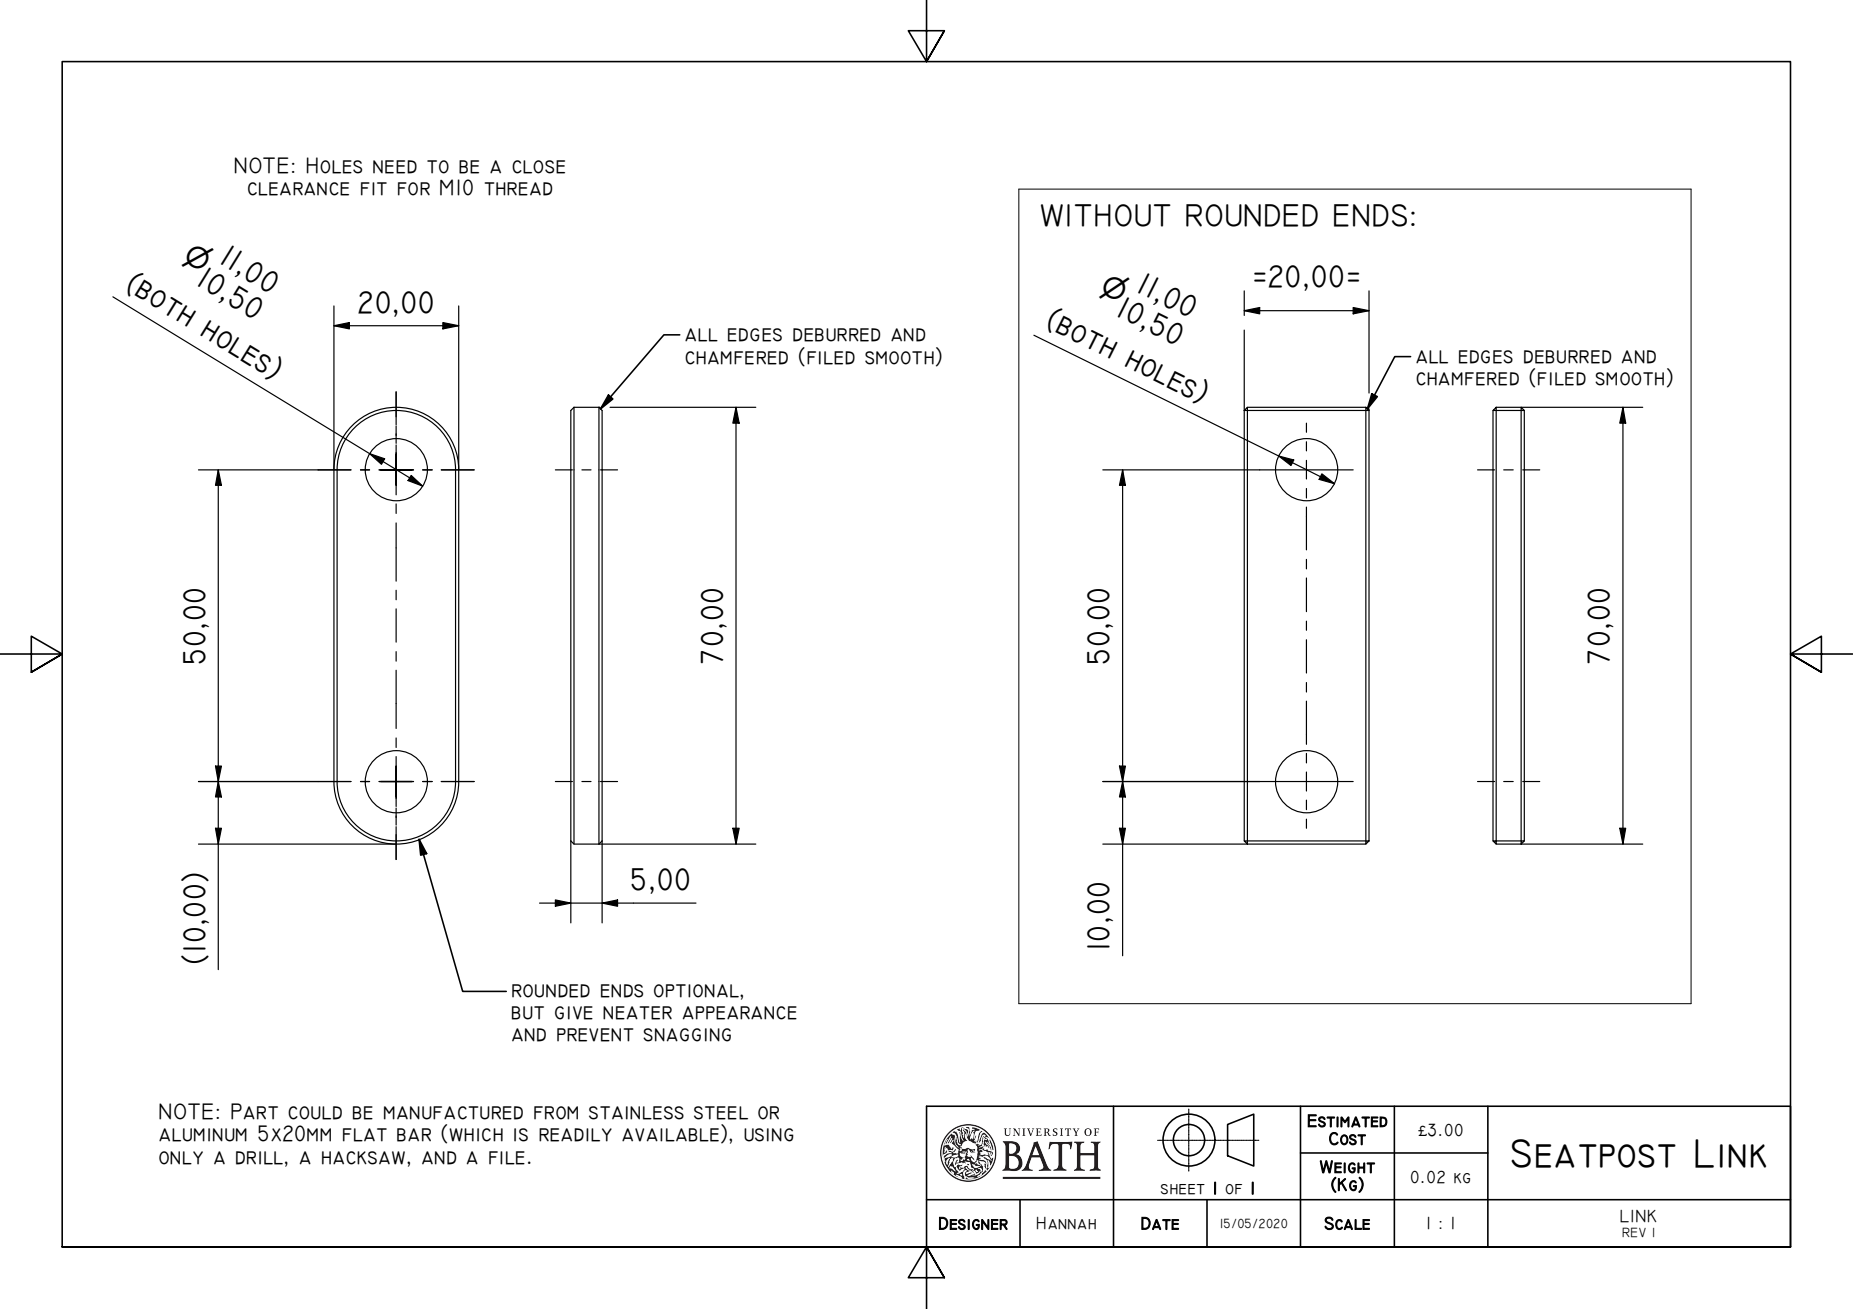
[picture p226: page 1]
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
