hannahrosen57/AdjustaBike-2.0/CAD/LINK 5.pdf

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

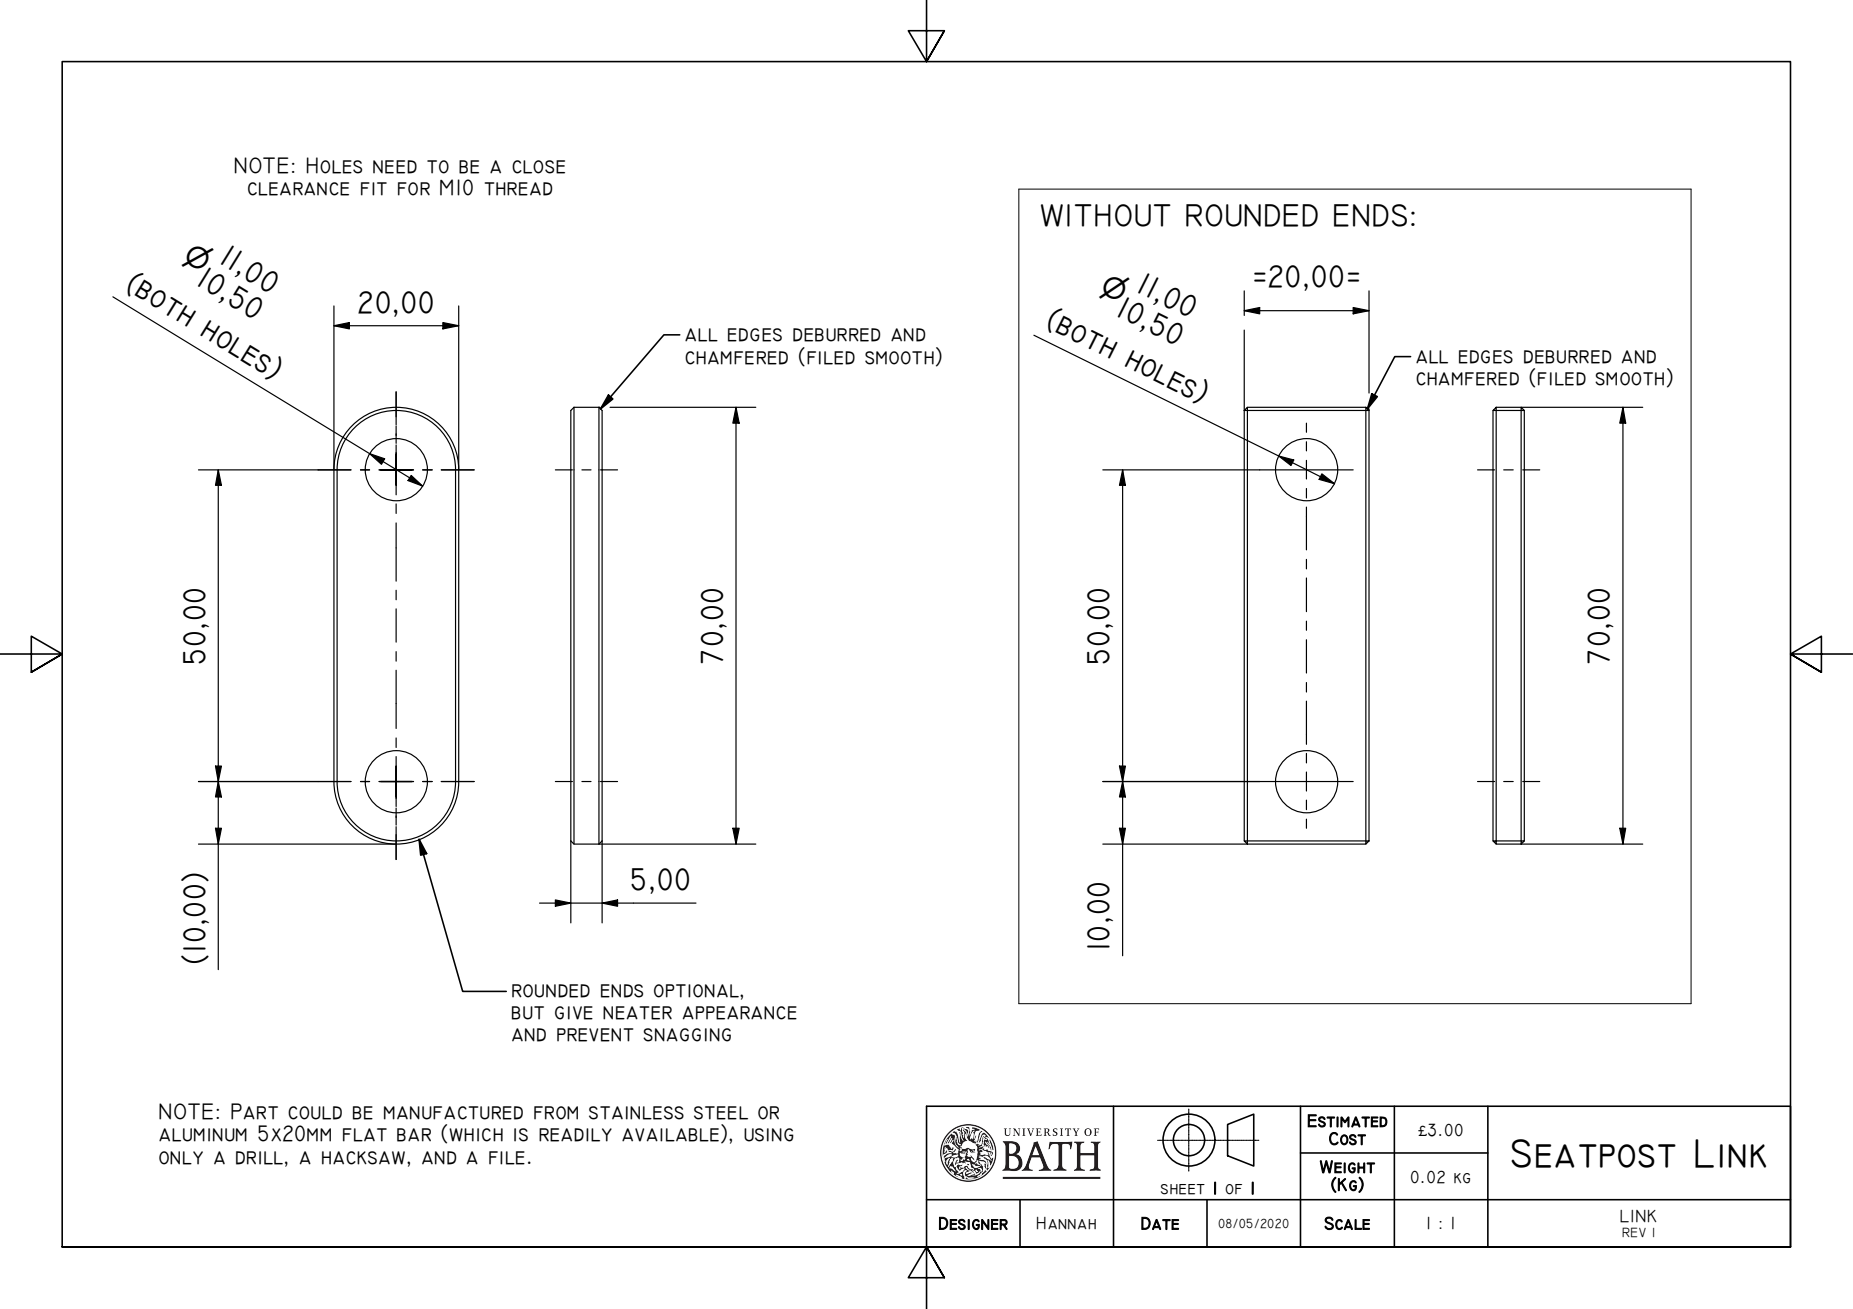
[picture p227: page 1]
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
