hannahrosen57/AdjustaBike-2.0/CAD/LINK 2.pdf

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

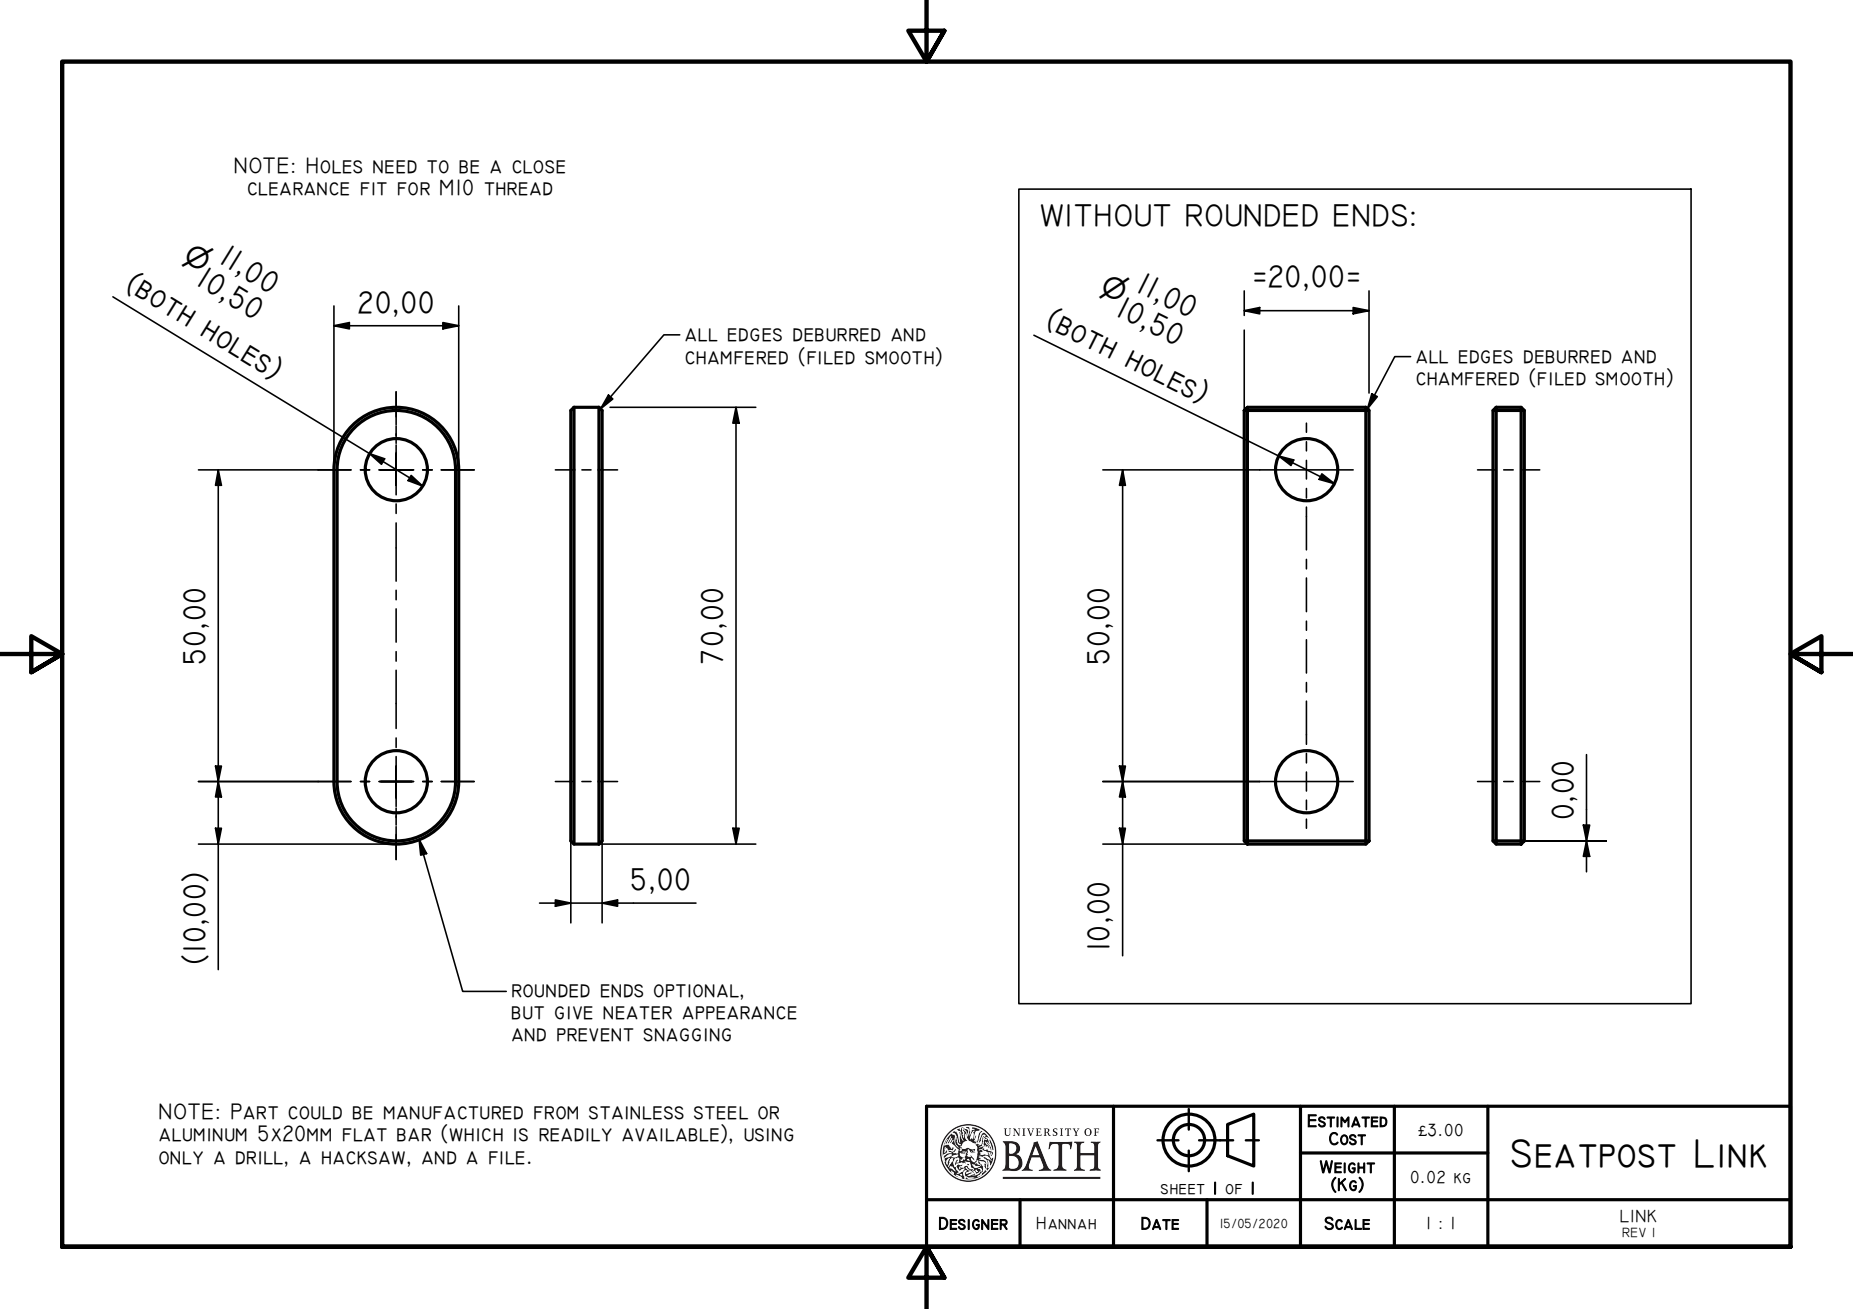
[picture p228: page 1]
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
