hannahrosen57/AdjustaBike-2.0/CAD/LINK.pdf

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

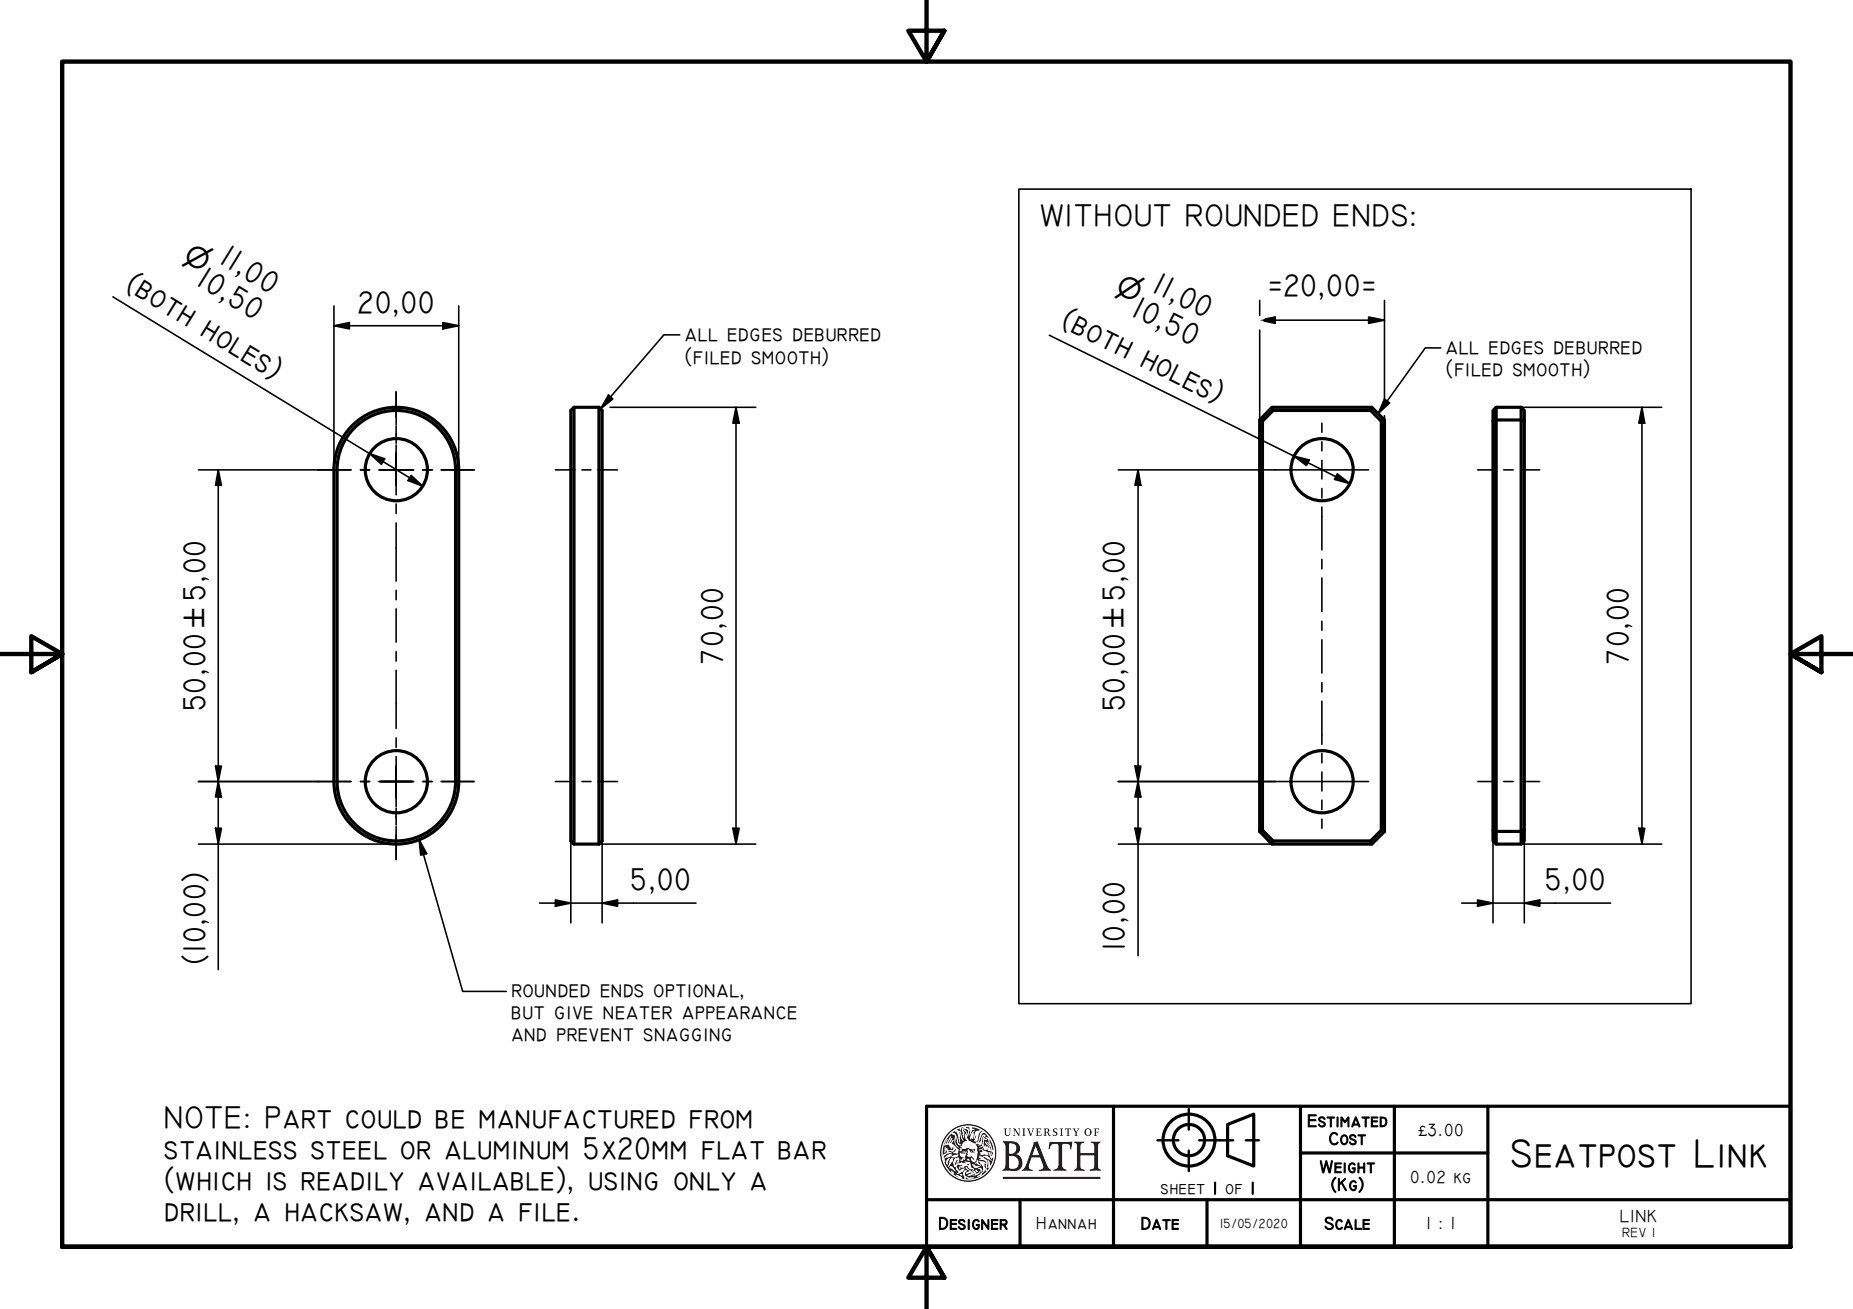
[picture p229: page 1]
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
