hannahrosen57/AdjustaBike-2.0/clutter/Example_Pack_1.pdf

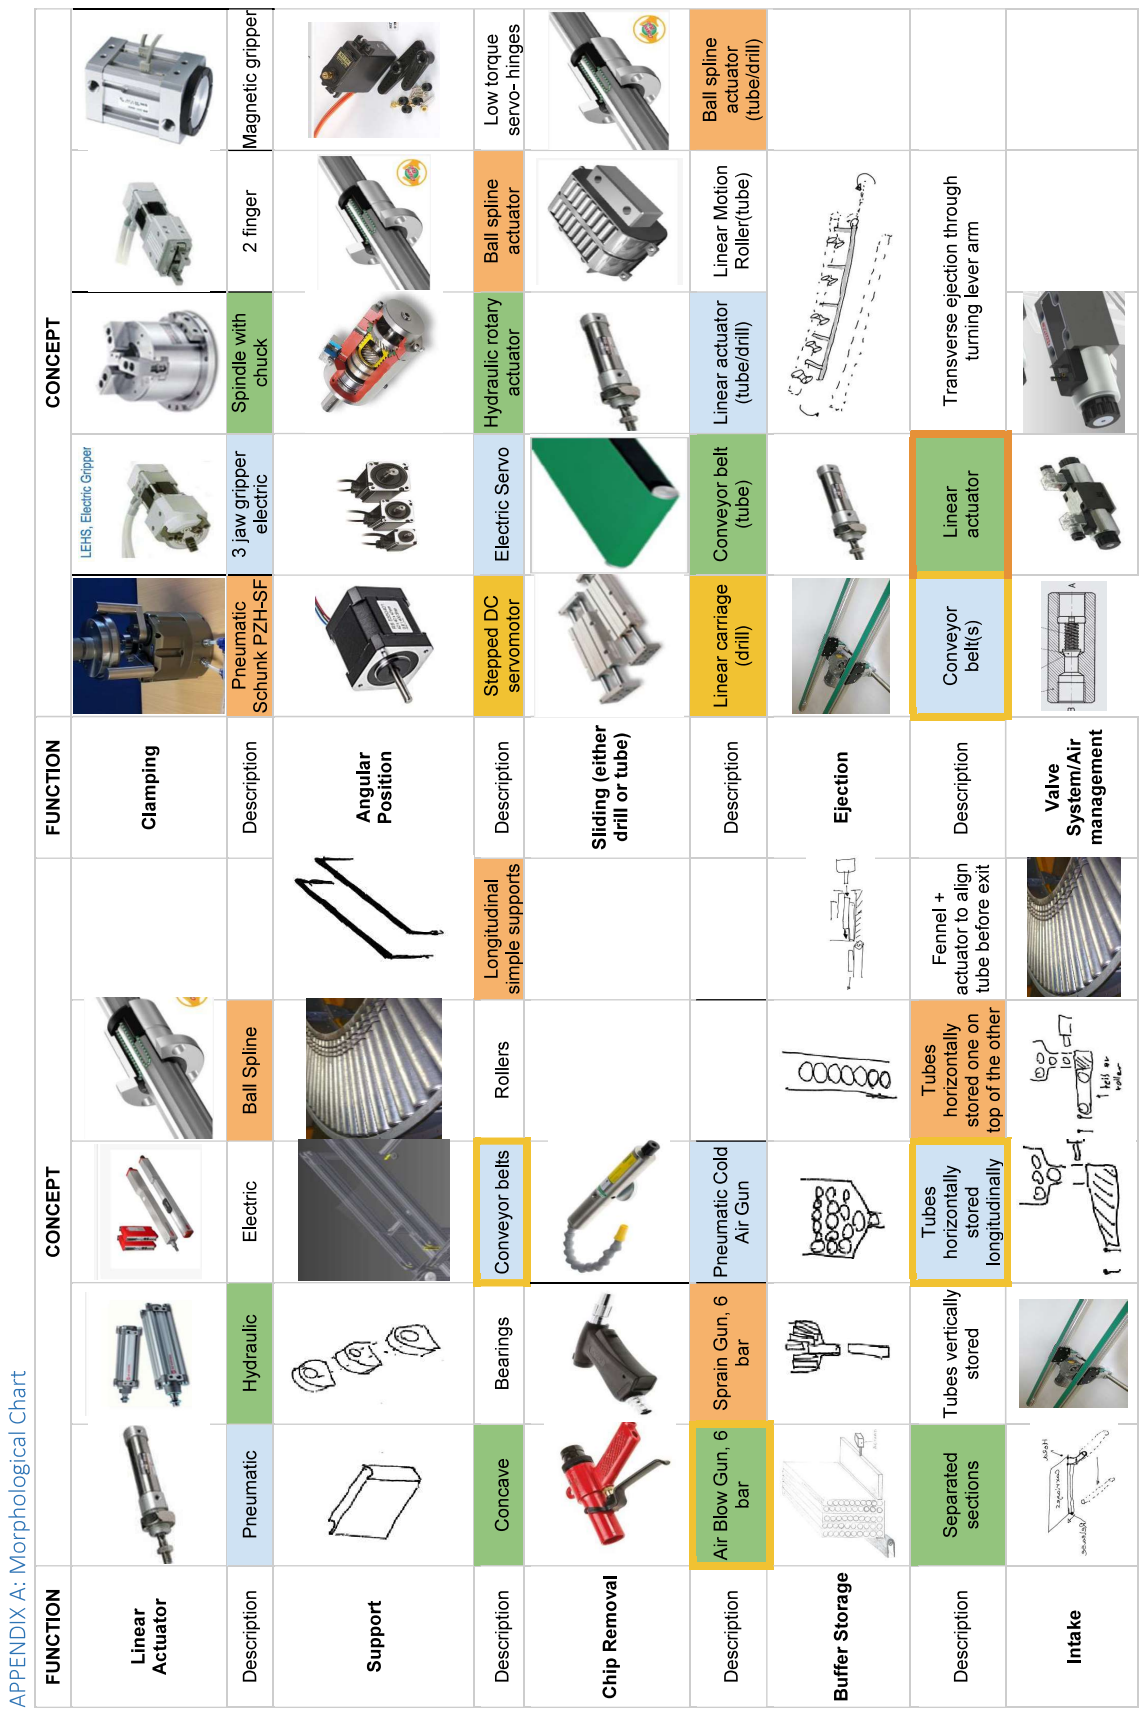
[picture p230: page 1]

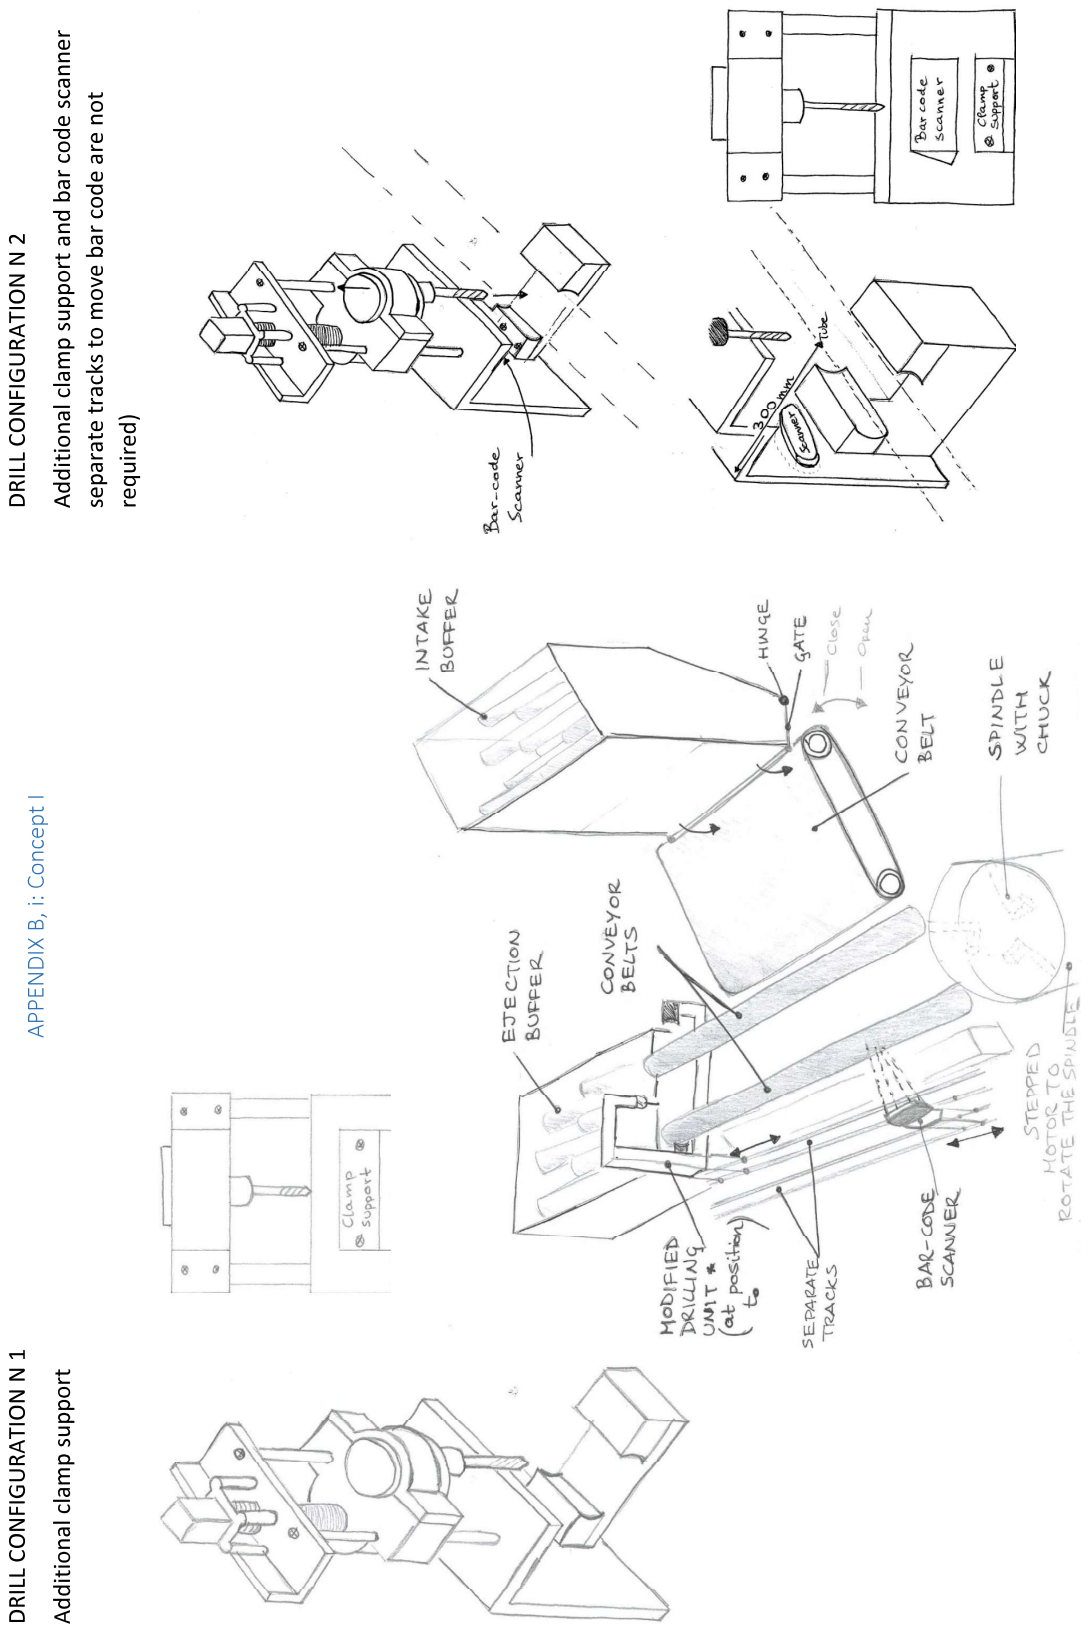
[picture p231: page 2]

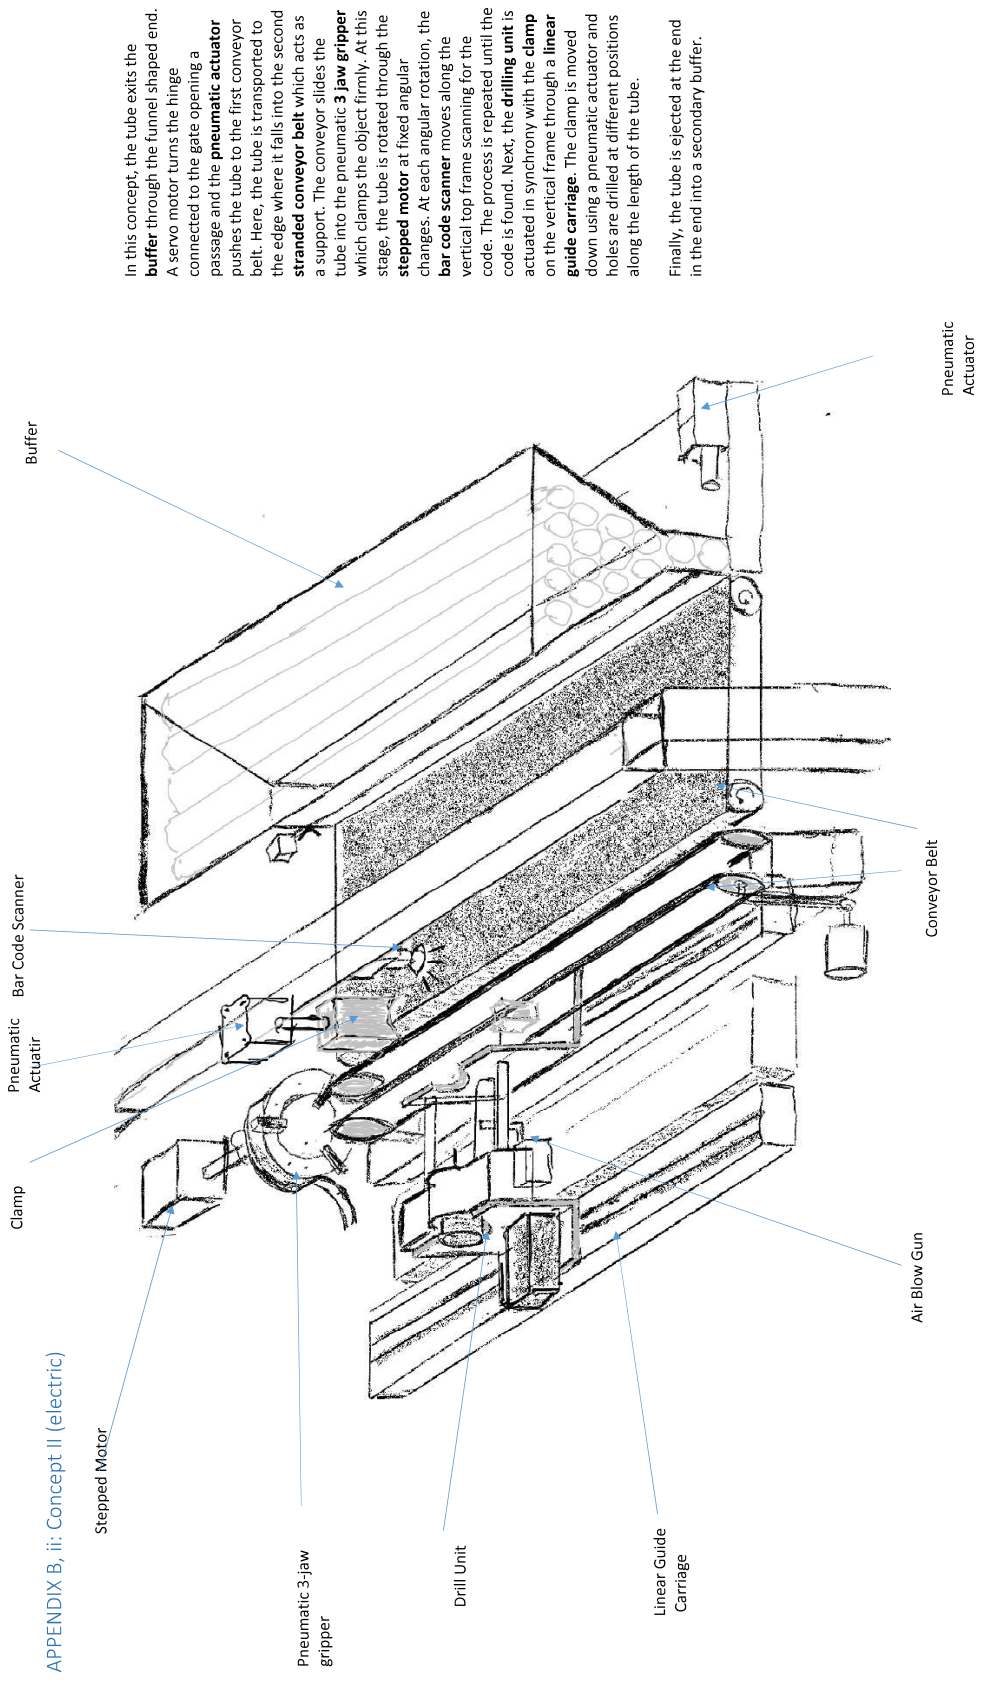
[picture p232: page 3]

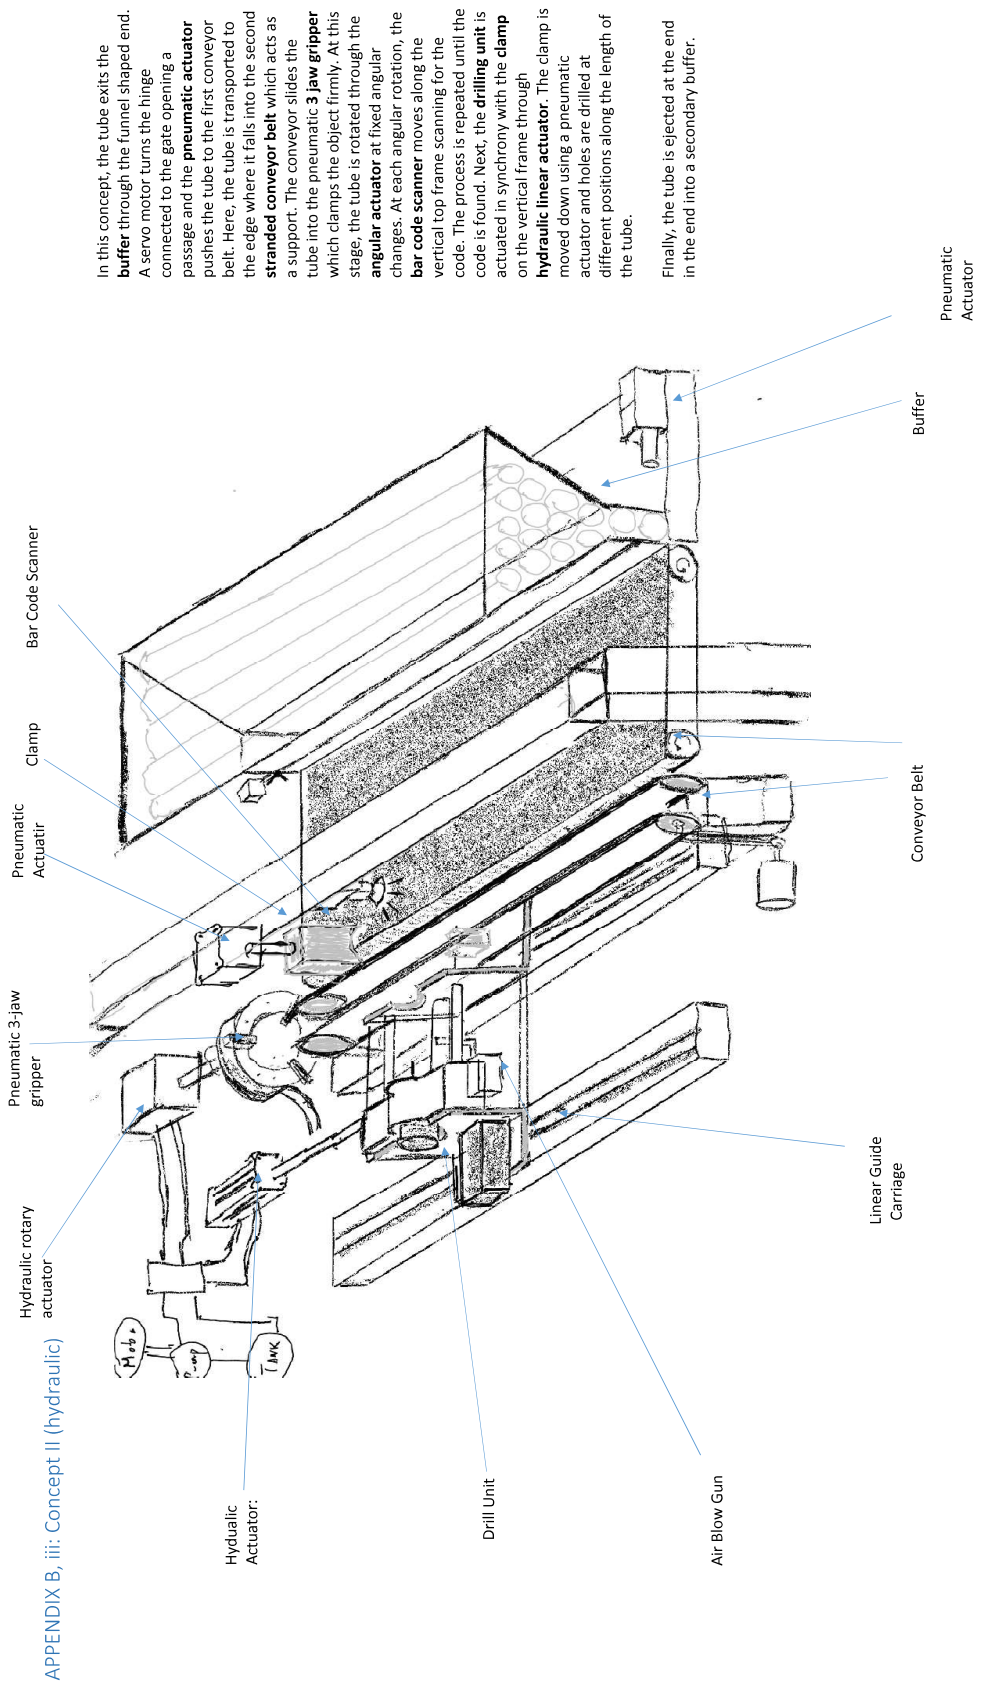
[picture p233: page 4]

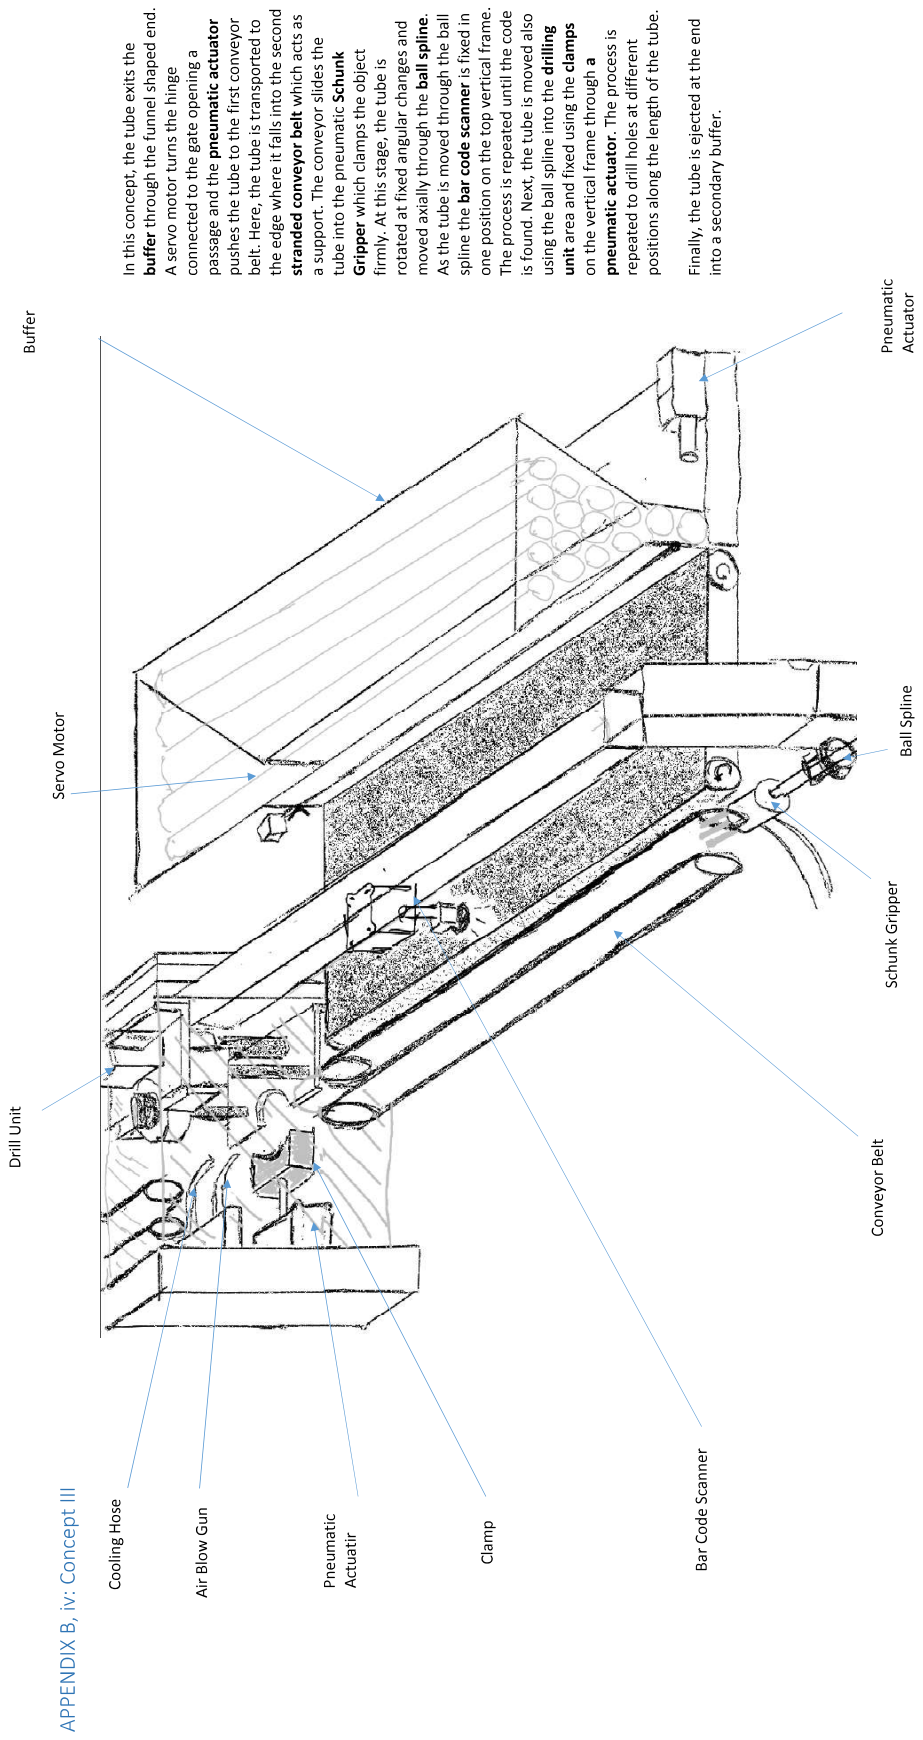
[picture p234: page 5]

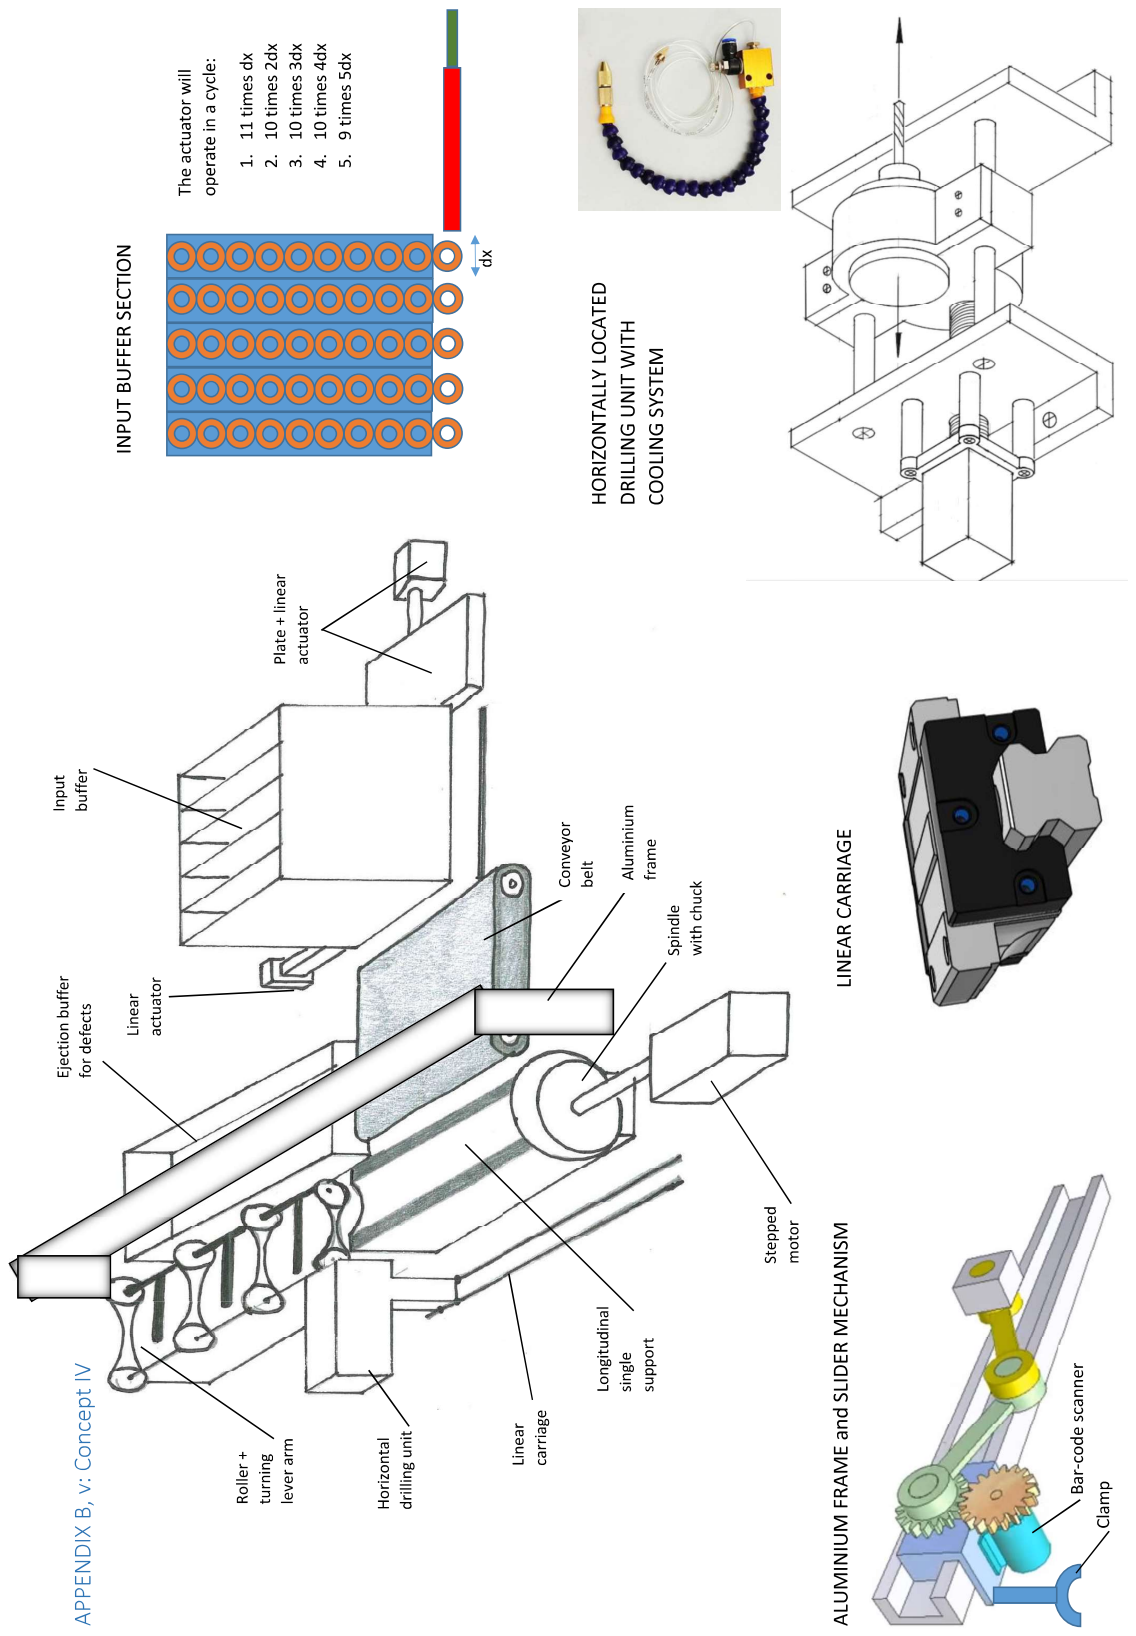
[picture p235: page 6]

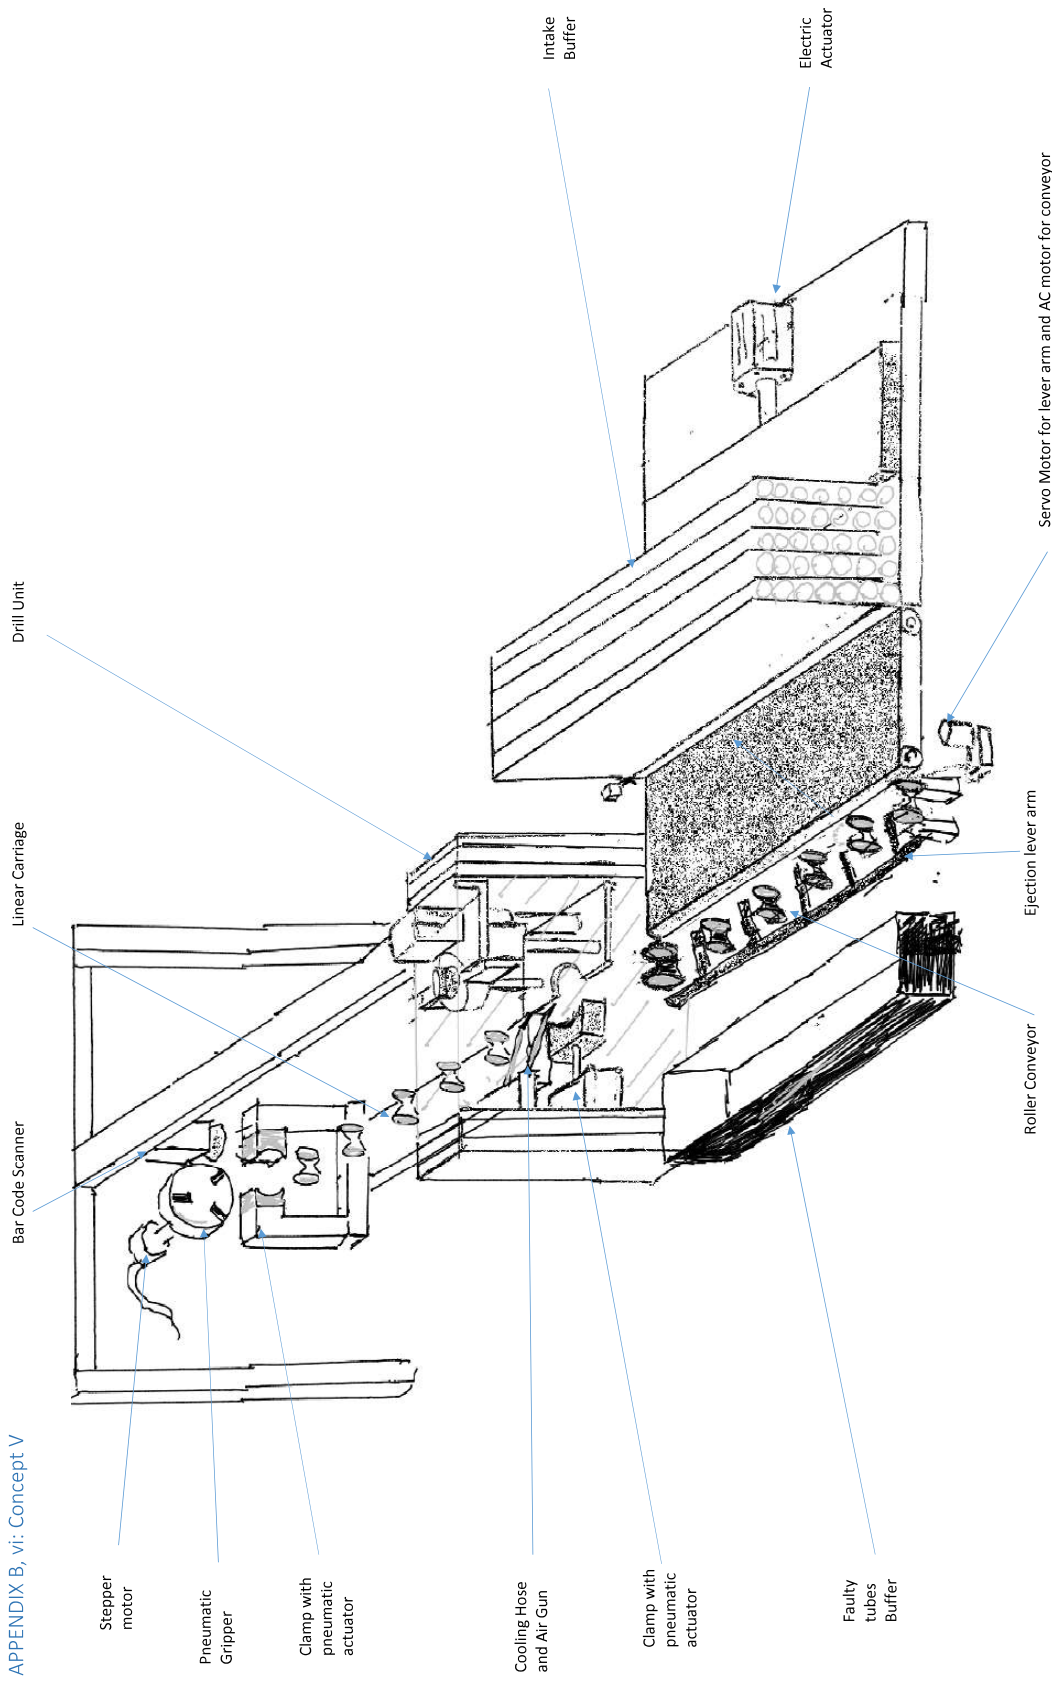
[picture p236: page 7]
